ahujaesh/keeb/images/256x256.png

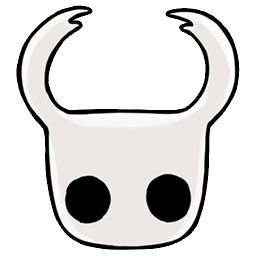
images/256x256.png
