ahujaesh/keeb/images/442066f4d0f0c367ef5b7a7e3e610547.jpg

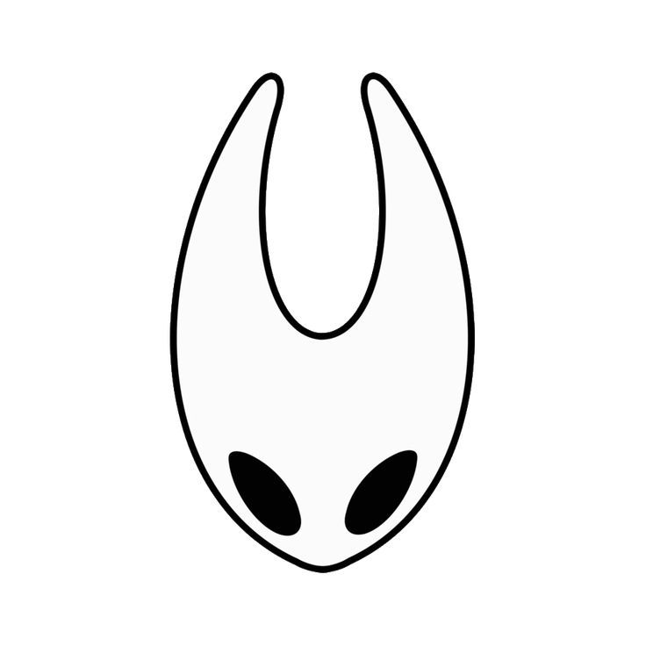
images/442066f4d0f0c367ef5b7a7e3e610547.jpg
