ahujaesh/keeb/images/Das_Shiekah_Auge_BoTW.png

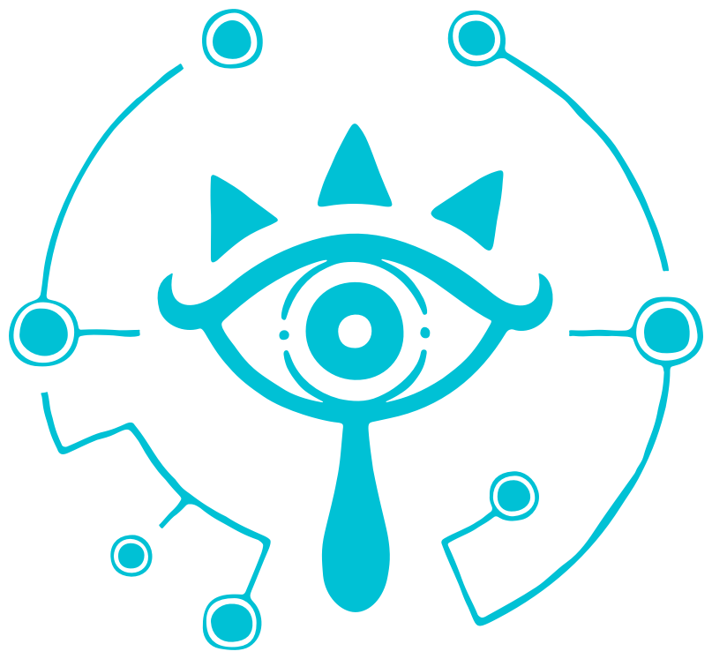
images/Das_Shiekah_Auge_BoTW.png
