ahujaesh/keeb/images/flag-standalone-wtransparent.png

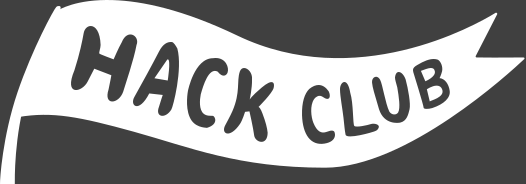
images/flag-standalone-wtransparent.png
