ahujaesh/keeb/marbastlib-main/marbastlib-main/resources/repolist.png

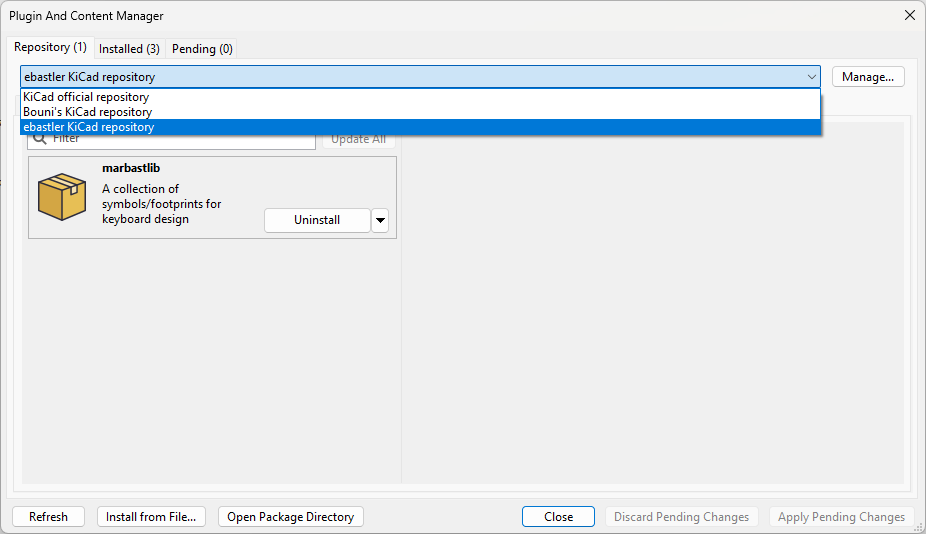
marbastlib-main/marbastlib-main/resources/repolist.png
