ahujaesh/keeb/misc/usb-a-female-2.snapshot.1/модуль USB A (2).JPG

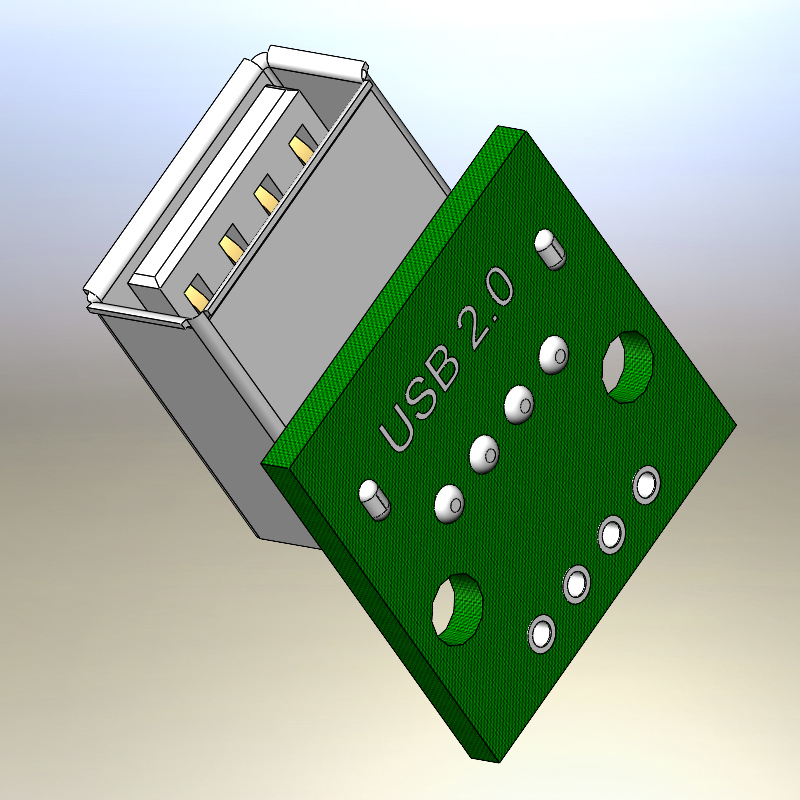
misc/usb-a-female-2.snapshot.1/модуль USB A (2).JPG
