ahujaesh/keeb/misc/usb-type-a-connector-2.snapshot.1/USB_Type_A rear.png

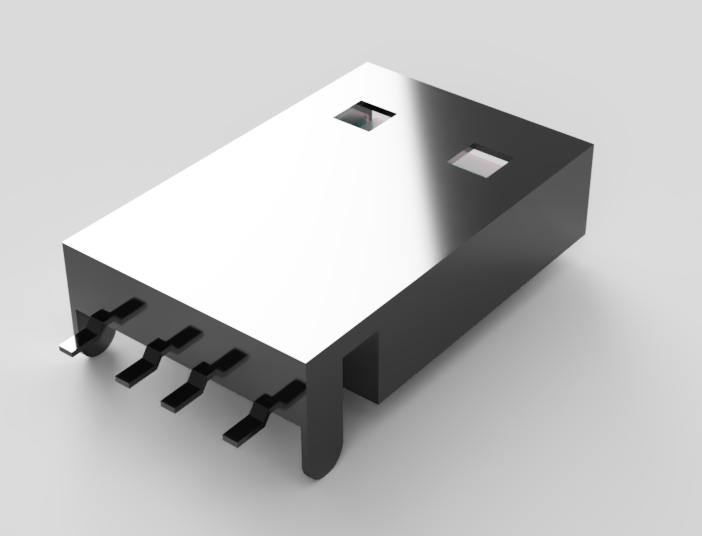
misc/usb-type-a-connector-2.snapshot.1/USB_Type_A rear.png
