ahujaesh/keeb/misc/usb-type-c-port-2.snapshot.1/USB Type C Port.png

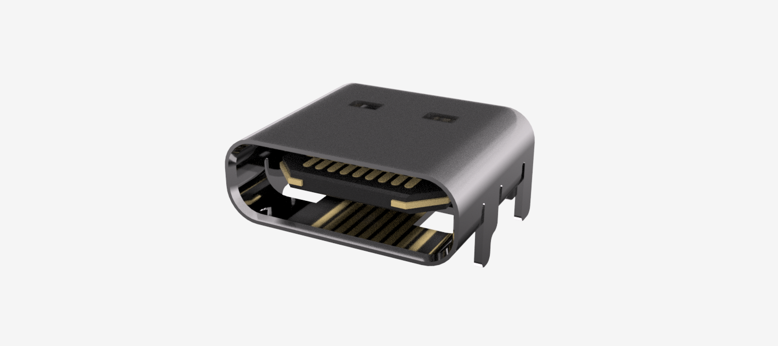
misc/usb-type-c-port-2.snapshot.1/USB Type C Port.png
