ahujaesh/keeb/misc/complete-cherry-mx-stem-keycap-set-optimized-for-3d-printing-gem-profile-multi-material-model_files/2.25U_ShiftyShiftL.3mf

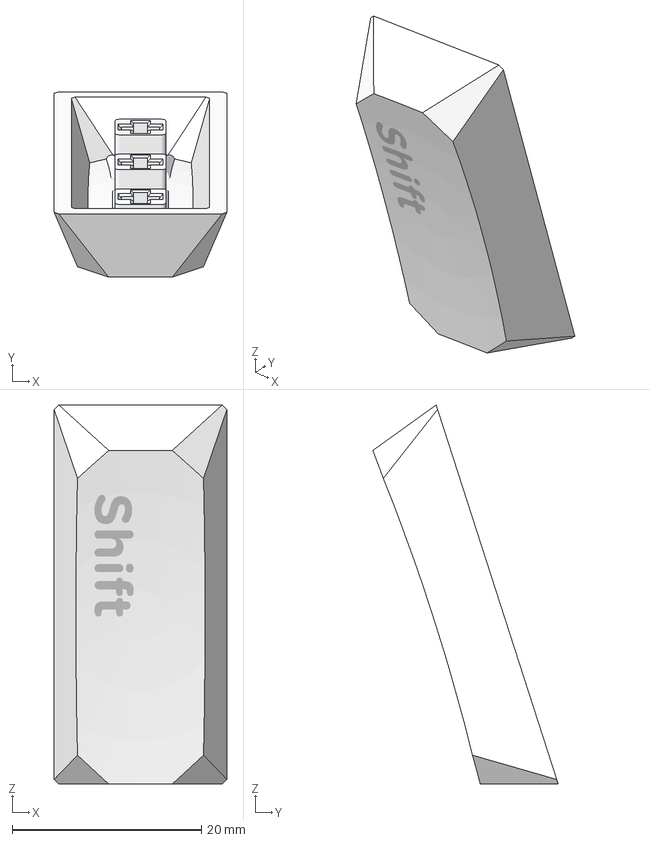
[picture p38: CAD file, 2025-10-08]
misc/complete-cherry-mx-stem-keycap-set-optimized-for-3d-printing-gem-profile-multi-material-model_files/2.25U_ShiftyShiftL.3mf
18.2 x 19.6 x 40.0 mm
