ahujaesh/keeb/marbastlib-main/marbastlib-main/3dmodels/CON_SM08B-SRSS-TB.step

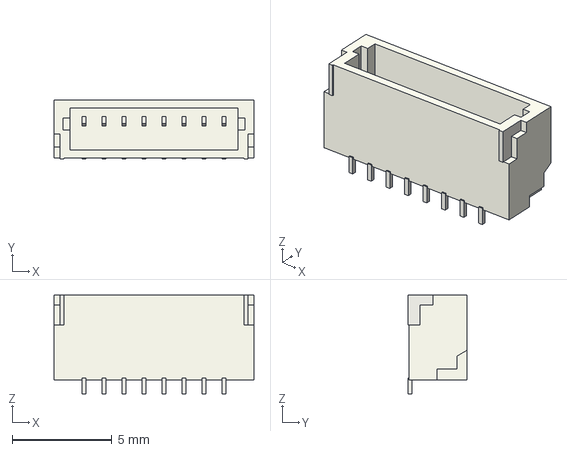
[picture p40: CAD file, 2025-10-04]
marbastlib-main/marbastlib-main/3dmodels/CON_SM08B-SRSS-TB.step
10.0 x 2.96 x 4.95 mm
