ahujaesh/keeb/marbastlib-main/marbastlib-main/3dmodels/CON_781710005.step

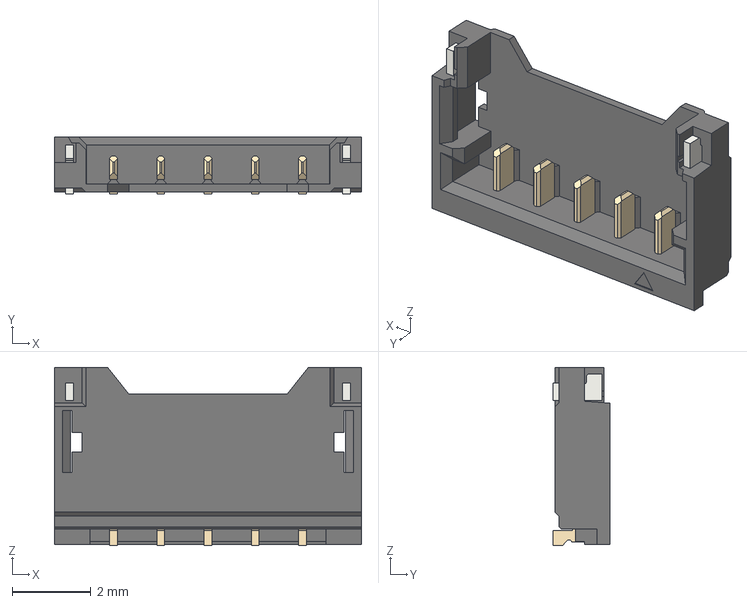
[picture p41: CAD file, 2025-10-04]
marbastlib-main/marbastlib-main/3dmodels/CON_781710005.step
7.80 x 1.45 x 4.53 mm
