ahujaesh/keeb/marbastlib-main/marbastlib-main/3dmodels/CON_2121340005.step

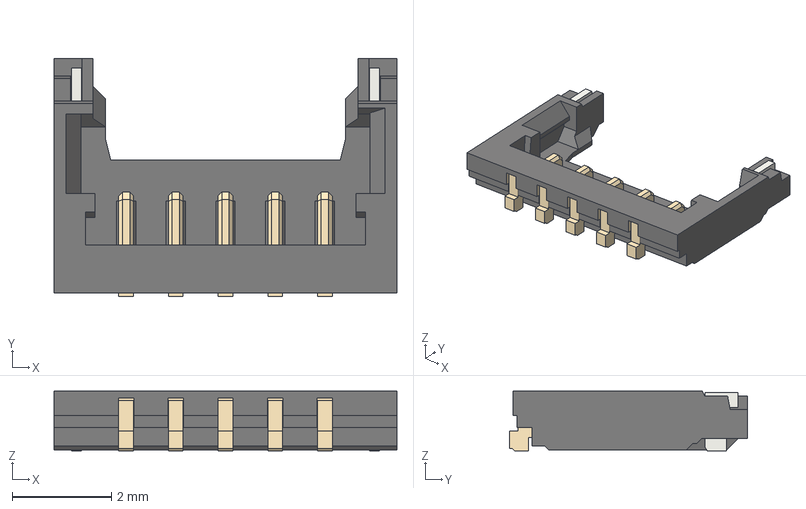
[picture p42: CAD file, 2025-10-04]
marbastlib-main/marbastlib-main/3dmodels/CON_2121340005.step
6.90 x 4.79 x 1.20 mm
