ahujaesh/keeb/marbastlib-main/marbastlib-main/3dmodels/HS_CPG135001S30_Choc.step

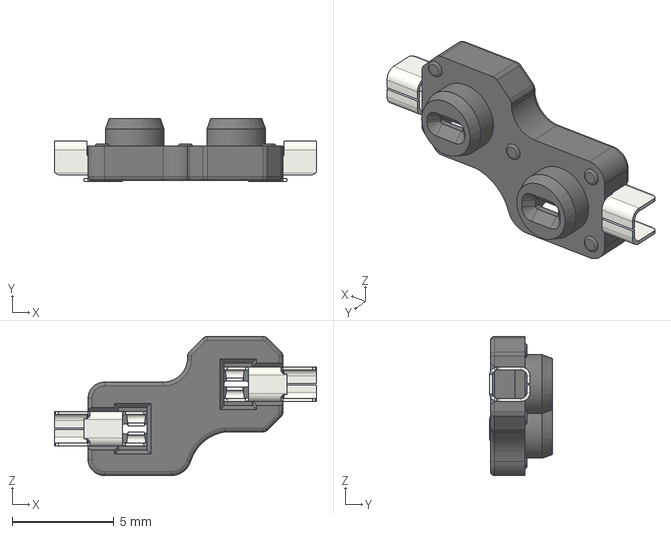
[picture p43: CAD file, 2025-10-04]
marbastlib-main/marbastlib-main/3dmodels/HS_CPG135001S30_Choc.step
12.9 x 3.09 x 6.85 mm
pin x 2
socket
