ahujaesh/keeb/marbastlib-main/marbastlib-main/3dmodels/CON_HytePro_M411P_Plug_1x04.step

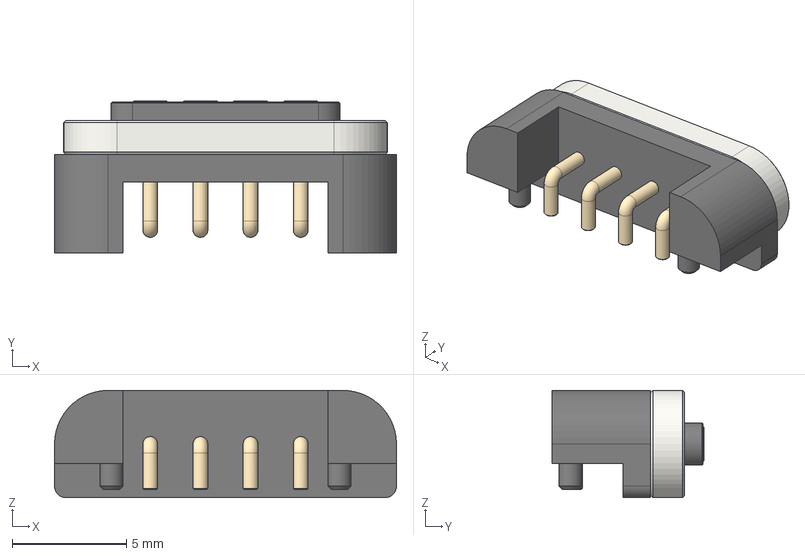
[picture p44: CAD file, 2025-10-04]
marbastlib-main/marbastlib-main/3dmodels/CON_HytePro_M411P_Plug_1x04.step
15.0 x 6.64 x 4.70 mm
Magnetic Connector Male - MiddlePart
Magnetic Connector Male - MountingPart
Magnetic Connector Male-tip_Standard
