ahujaesh/keeb/misc/complete-cherry-mx-stem-keycap-set-optimized-for-3d-printing-gem-profile-multi-material-model_files/numpad5.3mf

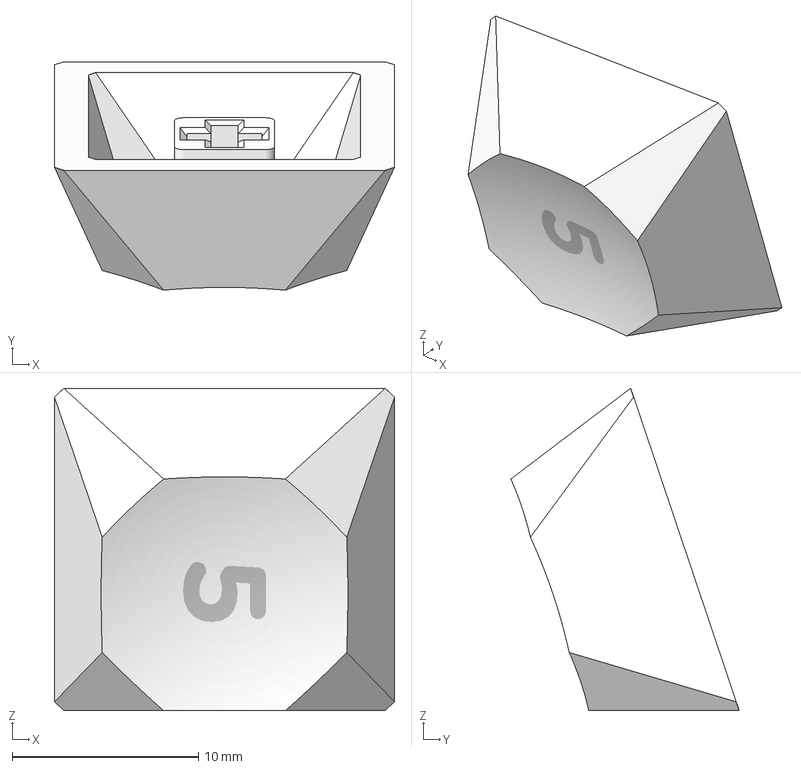
[picture p46: CAD file, 2025-10-08]
misc/complete-cherry-mx-stem-keycap-set-optimized-for-3d-printing-gem-profile-multi-material-model_files/numpad5.3mf
18.2 x 12.3 x 17.3 mm
