ahujaesh/keeb/marbastlib-main/marbastlib-main/3dmodels/CON_2082940030.step

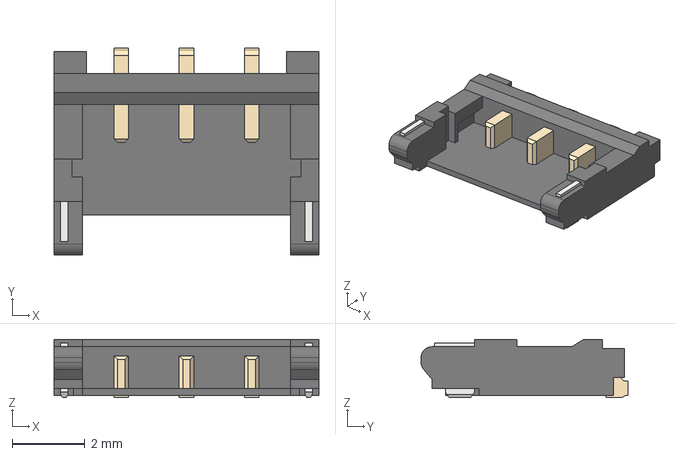
[picture p47: CAD file, 2025-10-04]
marbastlib-main/marbastlib-main/3dmodels/CON_2082940030.step
7.30 x 5.70 x 1.60 mm
