ahujaesh/keeb/marbastlib-main/marbastlib-main/3dmodels/PNT_RKJXU1210006.step

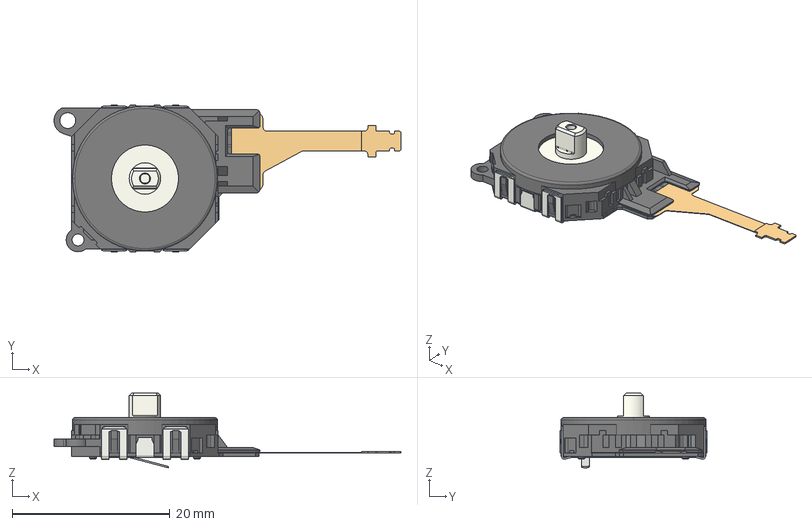
[picture p48: CAD file, 2025-10-04]
marbastlib-main/marbastlib-main/3dmodels/PNT_RKJXU1210006.step
44.0 x 18.6 x 9.50 mm
