ahujaesh/keeb/marbastlib-main/marbastlib-main/3dmodels/SW_ESP3020.step

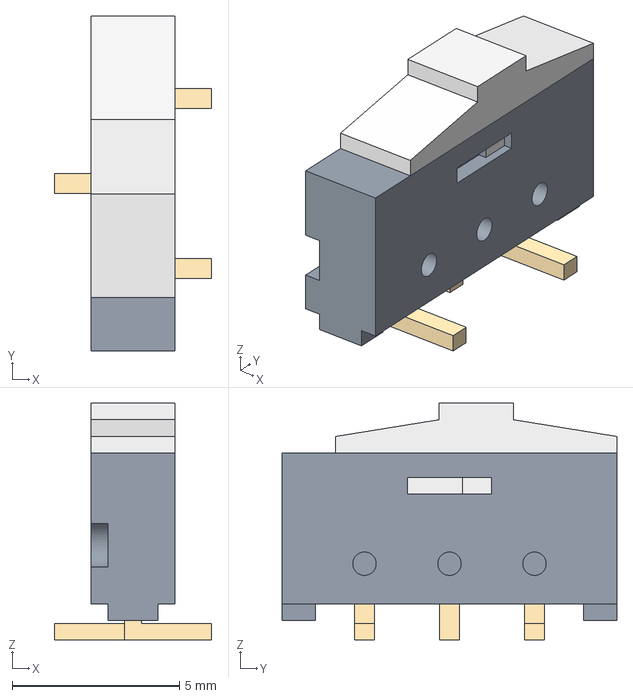
[picture p49: CAD file, 2025-10-04]
marbastlib-main/marbastlib-main/3dmodels/SW_ESP3020.step
4.70 x 10.0 x 7.08 mm
