ahujaesh/keeb/misc/complete-cherry-mx-stem-keycap-set-optimized-for-3d-printing-gem-profile-multi-material-model_files/2U_blank.3mf

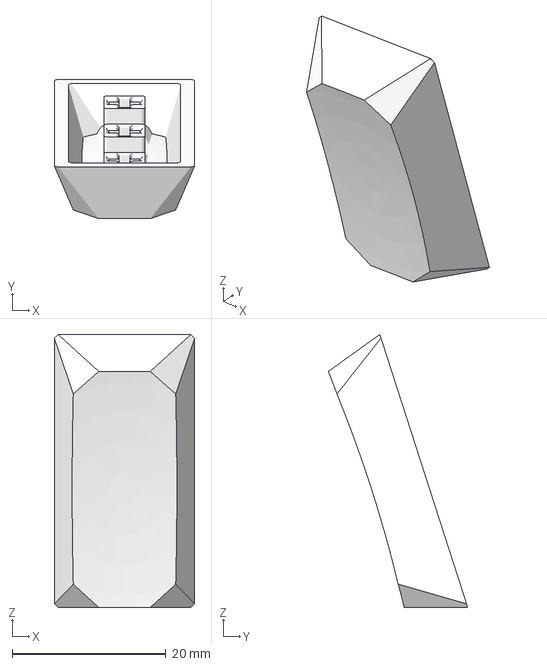
[picture p50: CAD file, 2025-10-08]
misc/complete-cherry-mx-stem-keycap-set-optimized-for-3d-printing-gem-profile-multi-material-model_files/2U_blank.3mf
18.2 x 18.1 x 35.5 mm
