ahujaesh/keeb/marbastlib-main/marbastlib-main/3dmodels/CON_2082940020.step

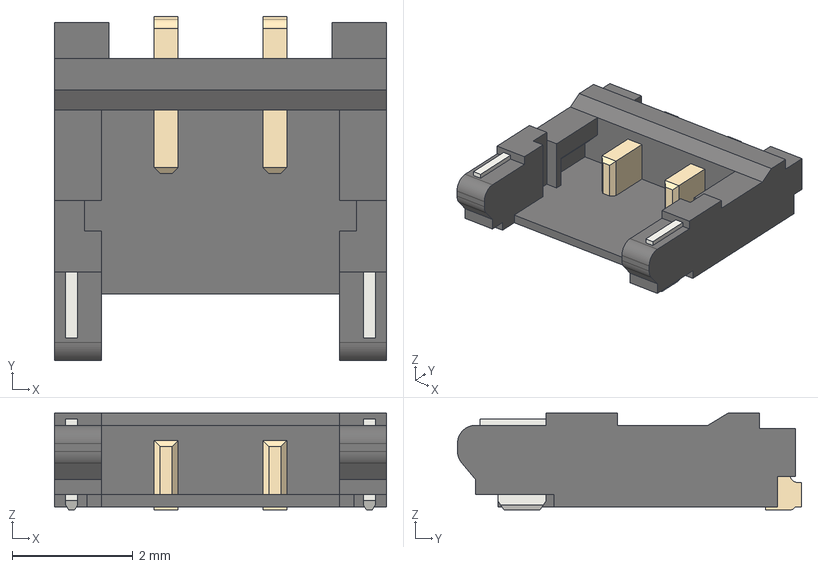
[picture p51: CAD file, 2025-10-04]
marbastlib-main/marbastlib-main/3dmodels/CON_2082940020.step
5.50 x 5.70 x 1.60 mm
