ahujaesh/keeb/marbastlib-main/marbastlib-main/3dmodels/L_Bourns_SRP6060FA.step

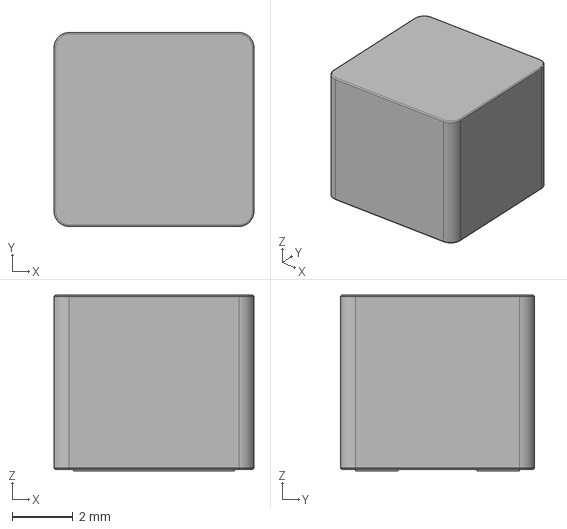
[picture p52: CAD file, 2025-10-04]
marbastlib-main/marbastlib-main/3dmodels/L_Bourns_SRP6060FA.step
6.60 x 6.40 x 5.80 mm
