ahujaesh/keeb/marbastlib-main/marbastlib-main/3dmodels/CON_781710003.step

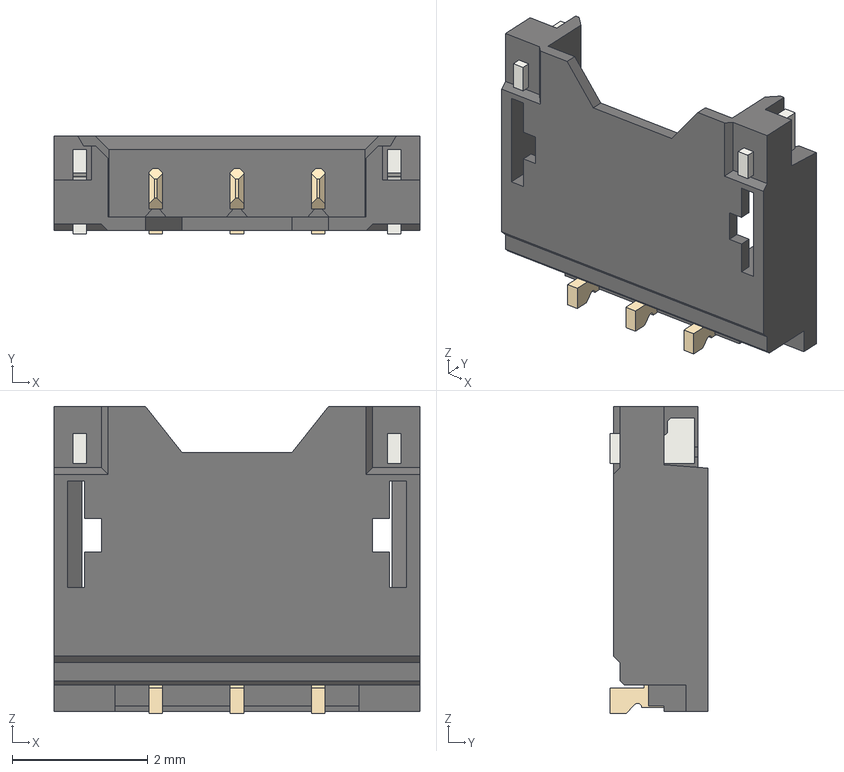
[picture p54: CAD file, 2025-10-04]
marbastlib-main/marbastlib-main/3dmodels/CON_781710003.step
5.40 x 1.45 x 4.53 mm
