ahujaesh/keeb/marbastlib-main/marbastlib-main/3dmodels/ROT_SKYLOONG_HS.step

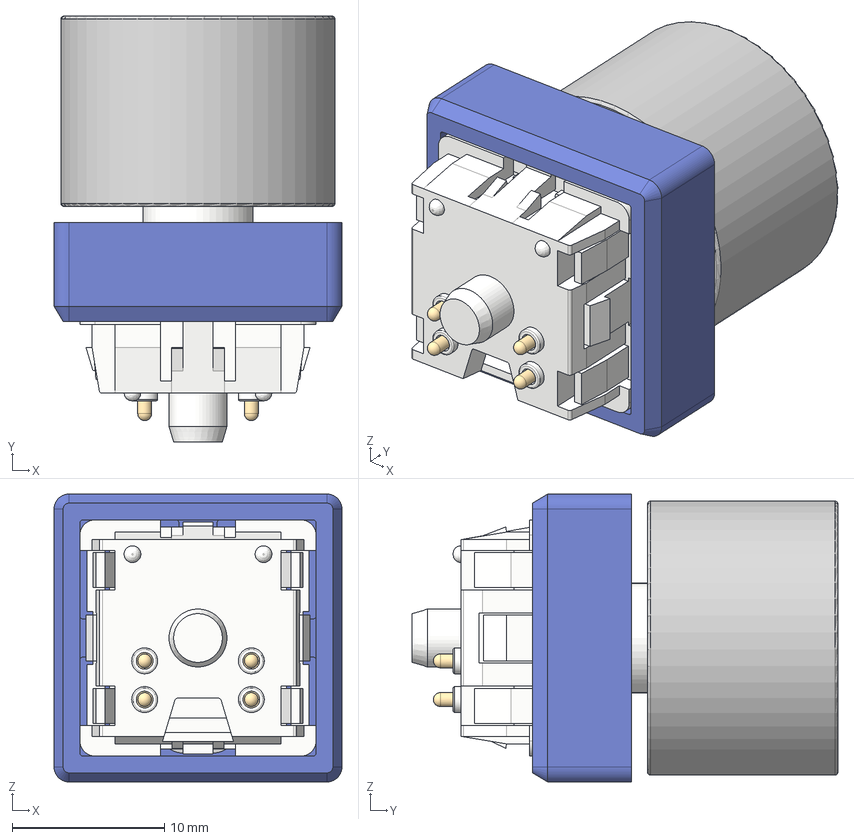
[picture p56: CAD file, 2025-10-04]
marbastlib-main/marbastlib-main/3dmodels/ROT_SKYLOONG_HS.step
18.9 x 27.9 x 18.9 mm
Top
Shaft
Pogo Pin x 4
Bottom
Top_1
Cover
Knob
