ahujaesh/keeb/misc/complete-cherry-mx-stem-keycap-set-optimized-for-3d-printing-gem-profile-multi-material-model_files/1.5U_LAlt.3mf

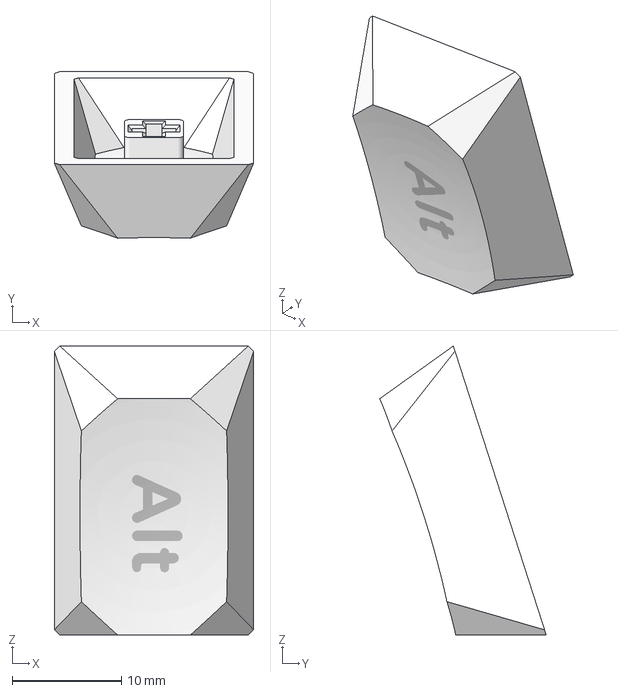
[picture p58: CAD file, 2025-10-08]
misc/complete-cherry-mx-stem-keycap-set-optimized-for-3d-printing-gem-profile-multi-material-model_files/1.5U_LAlt.3mf
18.2 x 15.2 x 26.4 mm
