ahujaesh/keeb/marbastlib-main/marbastlib-main/3dmodels/QFN-22_MP2722.step

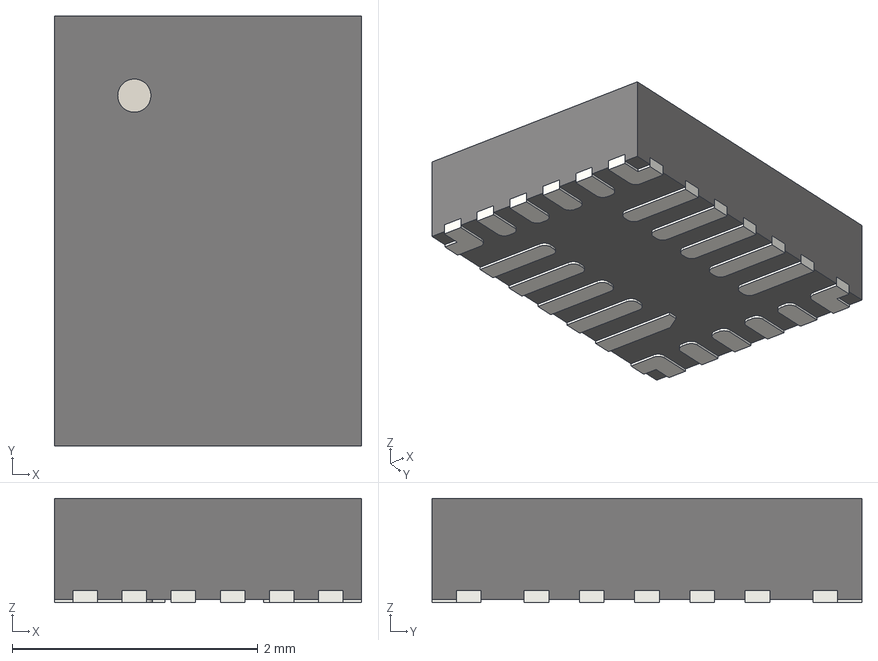
[picture p59: CAD file, 2025-10-04]
marbastlib-main/marbastlib-main/3dmodels/QFN-22_MP2722.step
2.50 x 3.50 x 0.85 mm
