ahujaesh/keeb/misc/complete-cherry-mx-stem-keycap-set-optimized-for-3d-printing-gem-profile-multi-material-model_files/1.25U_CommandSymbol.3mf

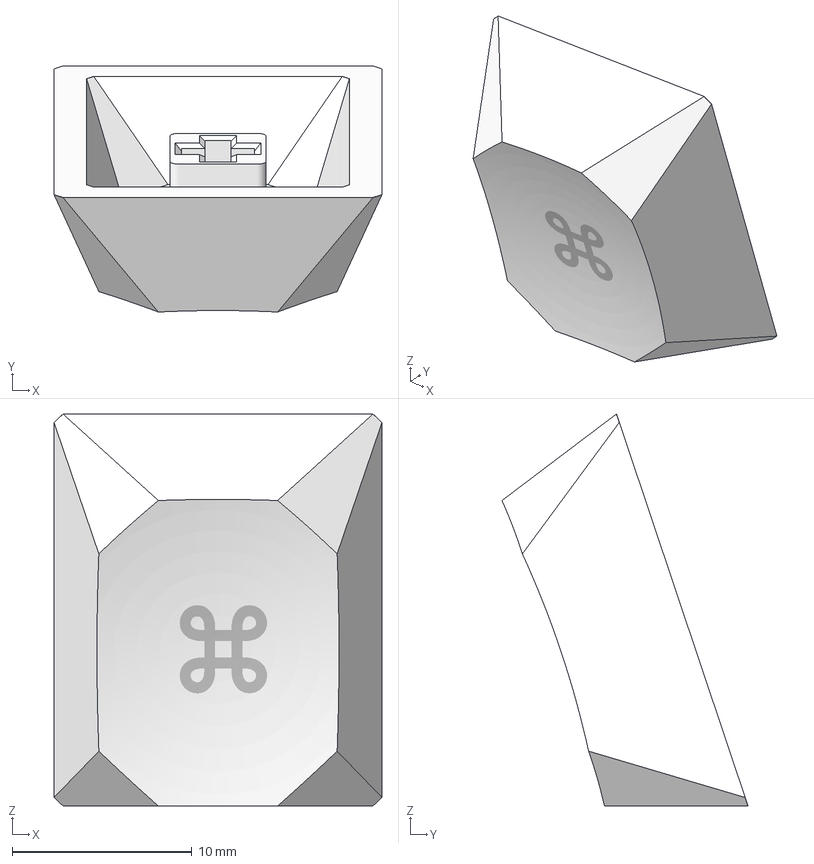
[picture p60: CAD file, 2025-10-08]
misc/complete-cherry-mx-stem-keycap-set-optimized-for-3d-printing-gem-profile-multi-material-model_files/1.25U_CommandSymbol.3mf
18.2 x 13.7 x 21.8 mm
