ahujaesh/keeb/marbastlib-main/marbastlib-main/3dmodels/CON_XUNPU_FPC-05F-24PH20.step

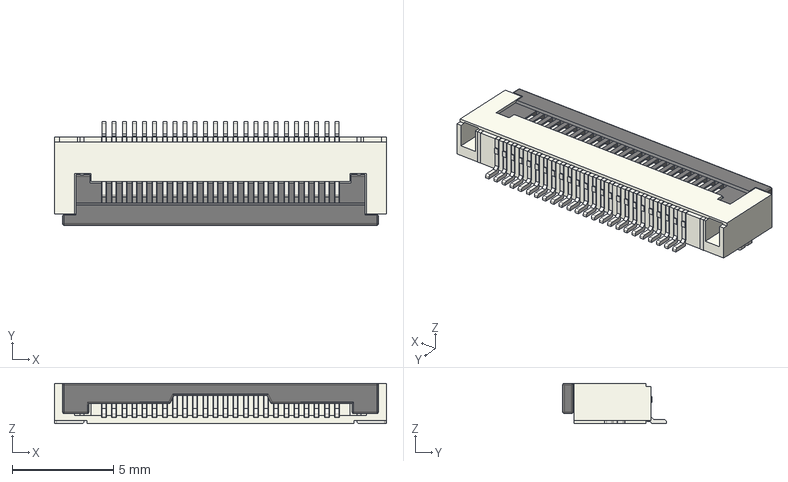
[picture p61: CAD file, 2025-10-04]
marbastlib-main/marbastlib-main/3dmodels/CON_XUNPU_FPC-05F-24PH20.step
16.4 x 5.12 x 2.00 mm
Board
