ahujaesh/keeb/marbastlib-main/marbastlib-main/3dmodels/CON_781710004.step

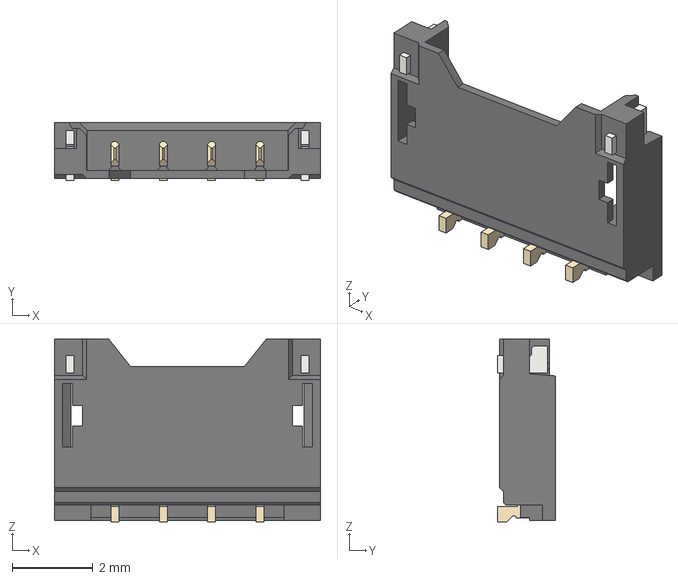
[picture p62: CAD file, 2025-10-04]
marbastlib-main/marbastlib-main/3dmodels/CON_781710004.step
6.60 x 1.45 x 4.53 mm
