ahujaesh/keeb/marbastlib-main/marbastlib-main/3dmodels/CON_781715006.step

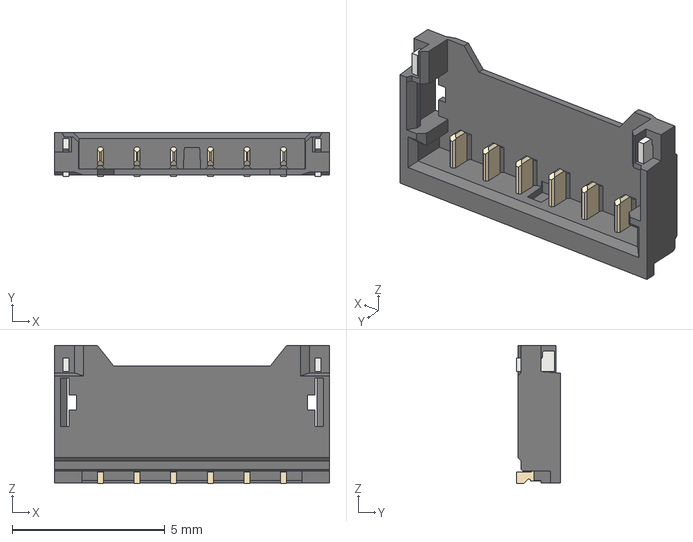
[picture p63: CAD file, 2025-10-04]
marbastlib-main/marbastlib-main/3dmodels/CON_781715006.step
9.00 x 1.45 x 4.53 mm
