ahujaesh/keeb/marbastlib-main/marbastlib-main/3dmodels/CON_781710002.step

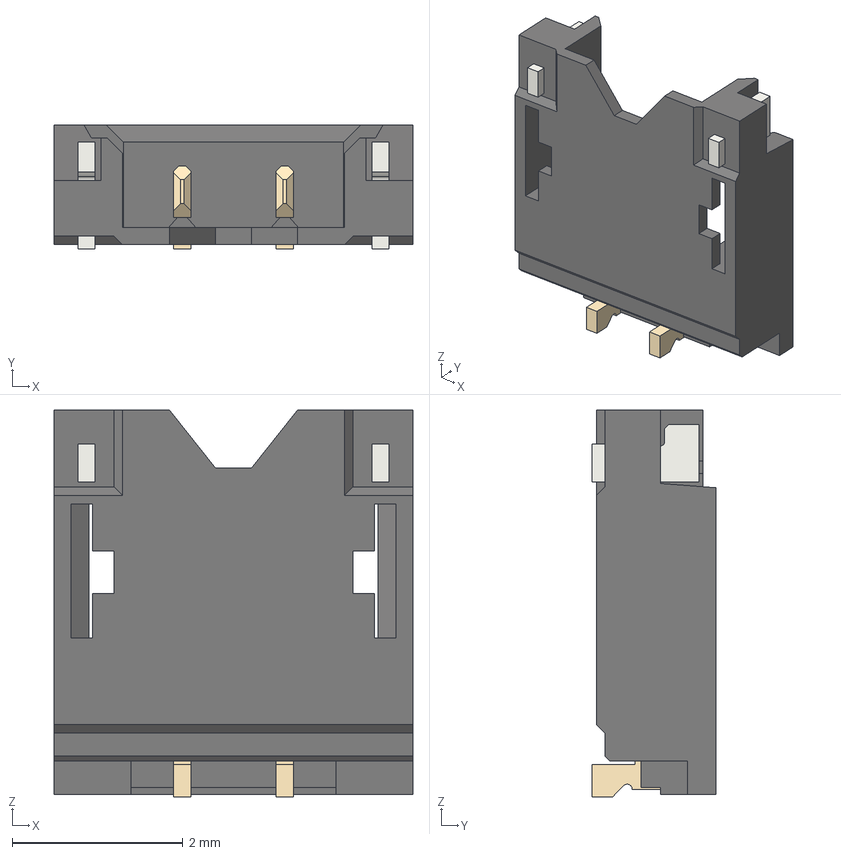
[picture p64: CAD file, 2025-10-04]
marbastlib-main/marbastlib-main/3dmodels/CON_781710002.step
4.20 x 1.45 x 4.53 mm
