ahujaesh/keeb/marbastlib-main/marbastlib-main/3dmodels/SW_SSSS223900.step

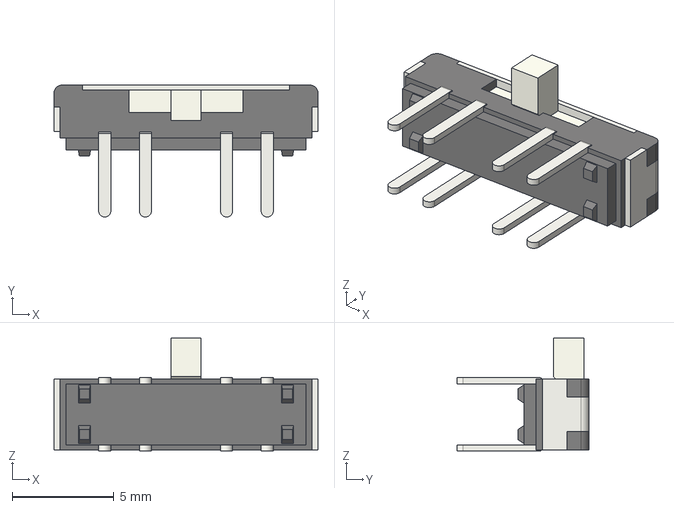
[picture p65: CAD file, 2025-10-04]
marbastlib-main/marbastlib-main/3dmodels/SW_SSSS223900.step
13.0 x 6.50 x 5.55 mm
