ahujaesh/keeb/marbastlib-main/marbastlib-main/3dmodels/L_Bourns_SRP6050CA.step

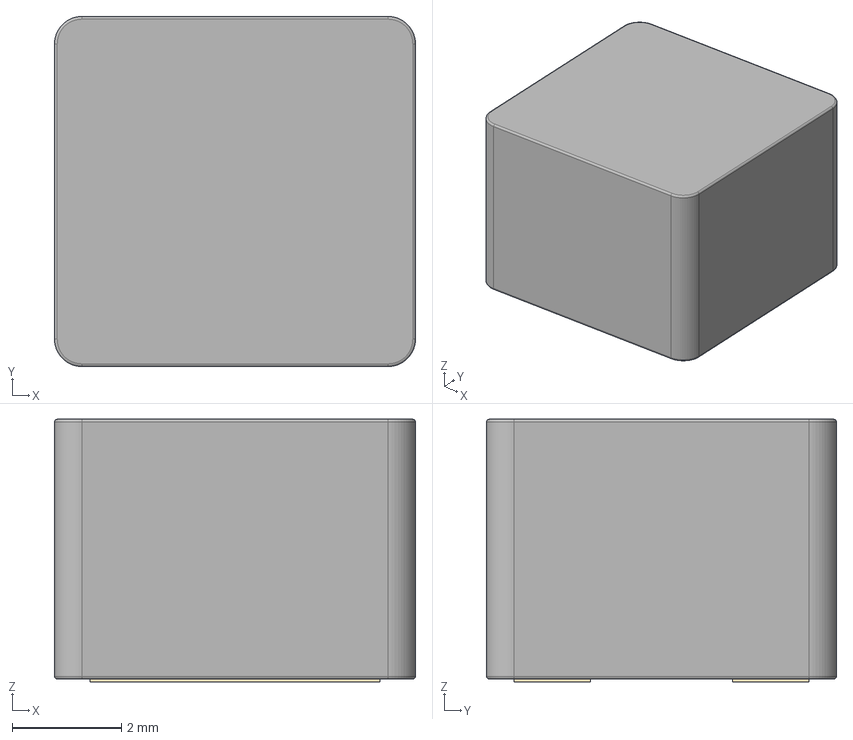
[picture p67: CAD file, 2025-10-04]
marbastlib-main/marbastlib-main/3dmodels/L_Bourns_SRP6050CA.step
6.60 x 6.40 x 4.80 mm
