ahujaesh/keeb/marbastlib-main/marbastlib-main/3dmodels/PNT_psp1000.step

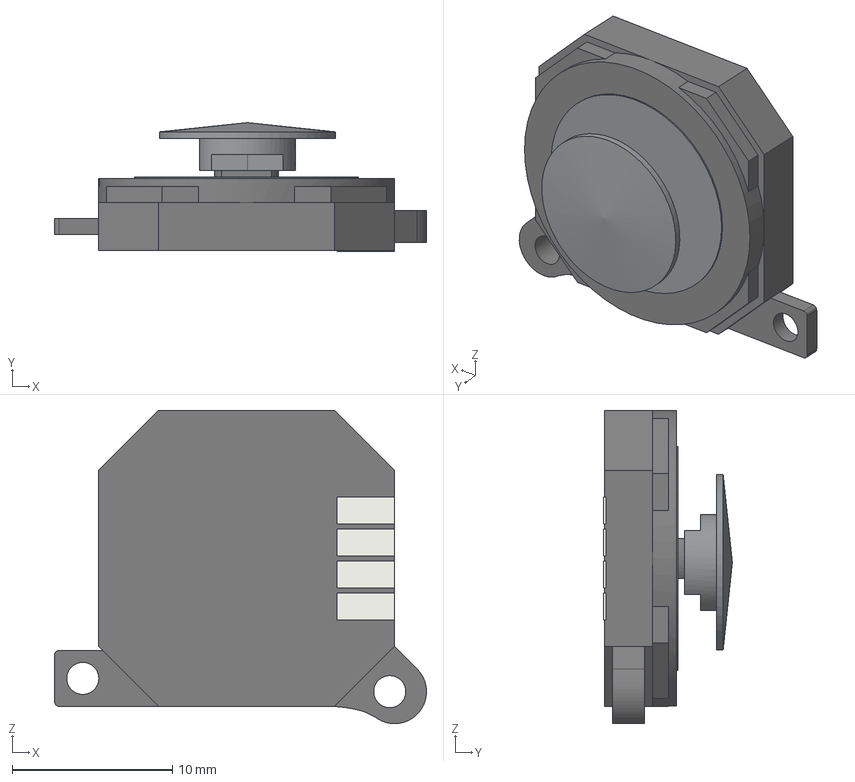
[picture p68: CAD file, 2025-10-04]
marbastlib-main/marbastlib-main/3dmodels/PNT_psp1000.step
23.2 x 8.05 x 19.6 mm
