ahujaesh/keeb/marbastlib-main/marbastlib-main/3dmodels/Liatris.step

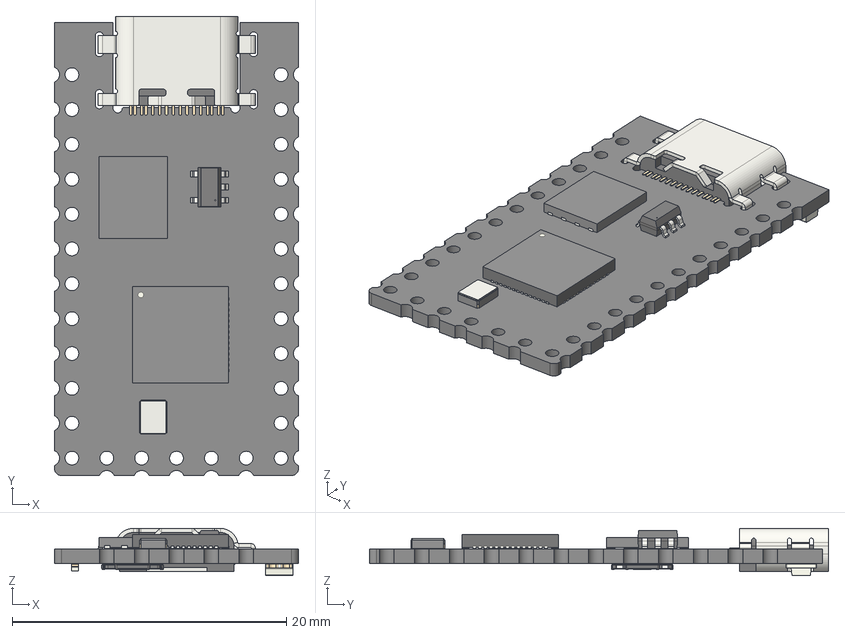
[picture p69: CAD file, 2025-10-04]
marbastlib-main/marbastlib-main/3dmodels/Liatris.step
17.8 x 33.5 x 3.44 mm
RP2040 PCB
