ahujaesh/keeb/marbastlib-main/marbastlib-main/3dmodels/LED_SK6812MINI-E.step

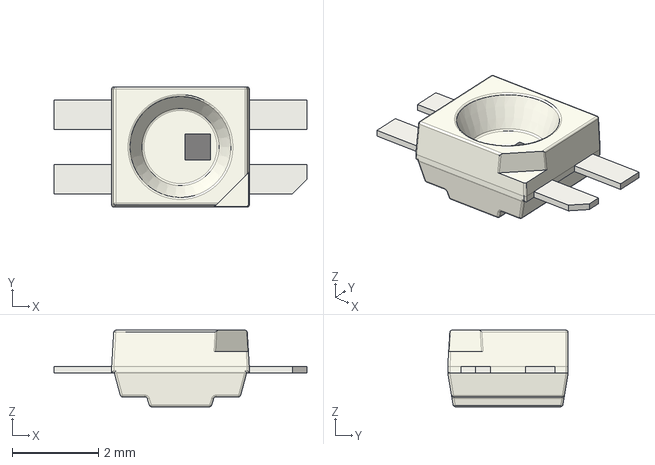
[picture p71: CAD file, 2025-10-04]
marbastlib-main/marbastlib-main/3dmodels/LED_SK6812MINI-E.step
5.88 x 2.80 x 1.78 mm
