ahujaesh/keeb/marbastlib-main/marbastlib-main/3dmodels/SW_SKHLLC.step

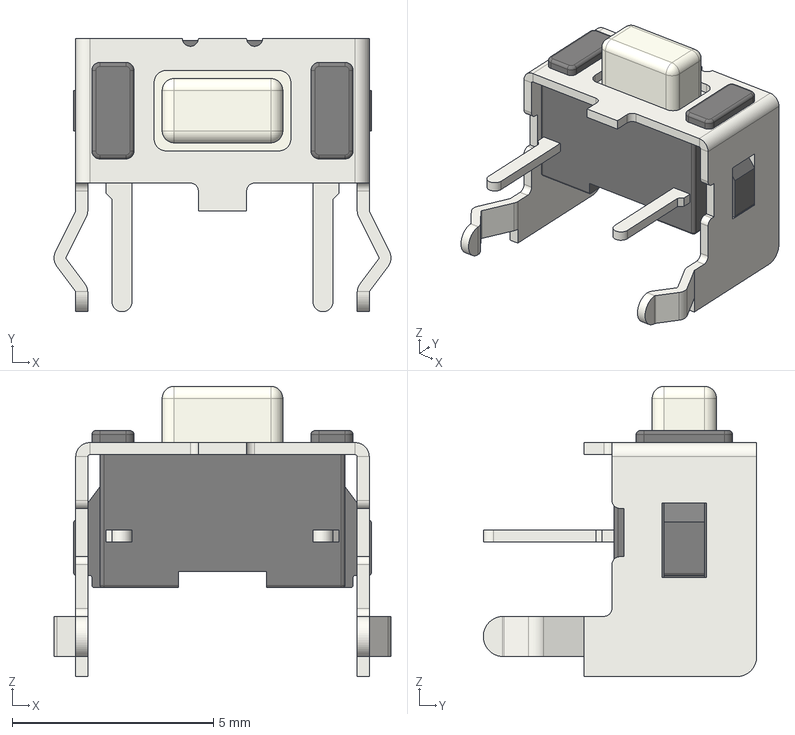
[picture p72: CAD file, 2025-10-04]
marbastlib-main/marbastlib-main/3dmodels/SW_SKHLLC.step
8.38 x 6.80 x 7.22 mm
