ahujaesh/keeb/marbastlib-main/marbastlib-main/3dmodels/CON_2082940050.step

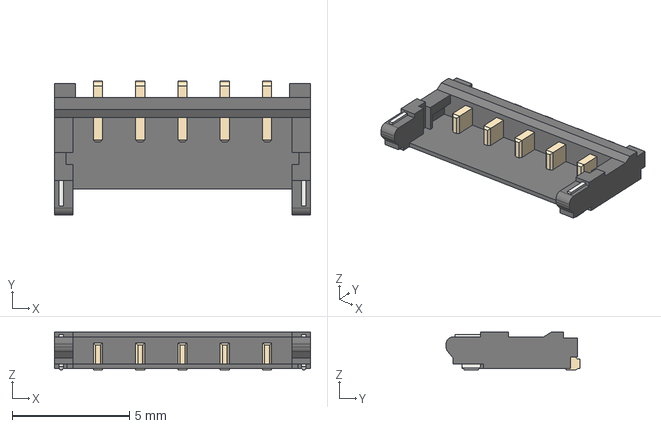
[picture p74: CAD file, 2025-10-04]
marbastlib-main/marbastlib-main/3dmodels/CON_2082940050.step
10.9 x 5.70 x 1.60 mm
