ahujaesh/keeb/marbastlib-main/marbastlib-main/3dmodels/CON_SM02B-SRSS-TB.step

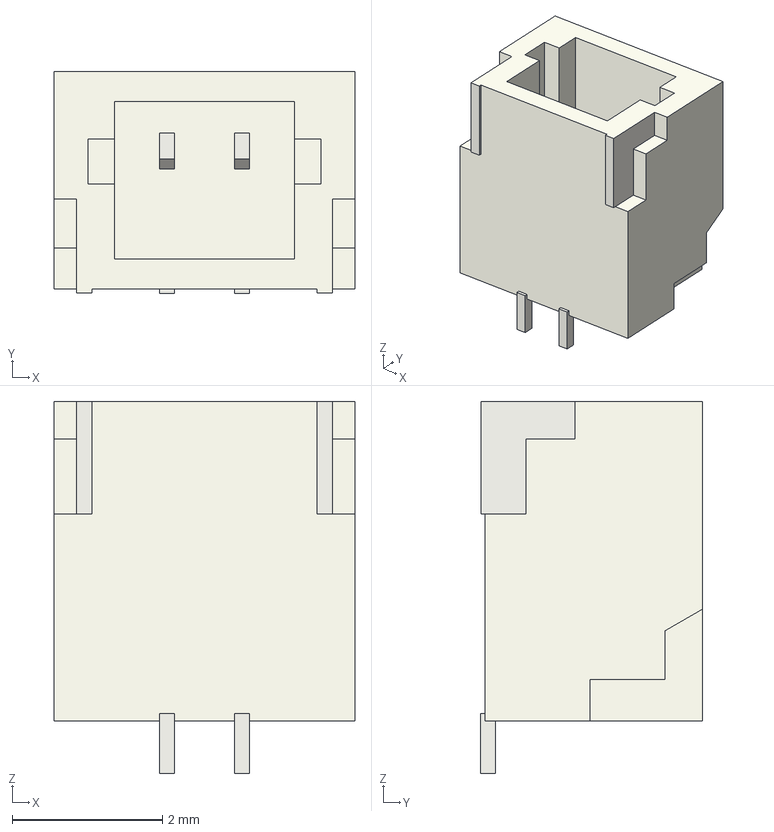
[picture p75: CAD file, 2025-10-04]
marbastlib-main/marbastlib-main/3dmodels/CON_SM02B-SRSS-TB.step
4.00 x 2.96 x 4.95 mm
