ahujaesh/keeb/marbastlib-main/marbastlib-main/3dmodels/PDFN3.3x3.3.step

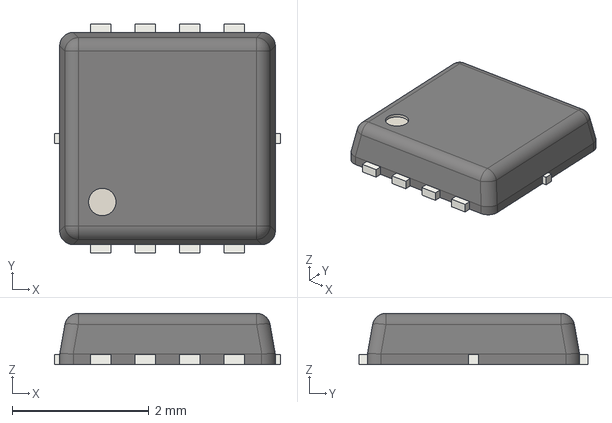
[picture p76: CAD file, 2025-10-04]
marbastlib-main/marbastlib-main/3dmodels/PDFN3.3x3.3.step
3.30 x 3.35 x 0.75 mm
