ahujaesh/keeb/marbastlib-main/marbastlib-main/3dmodels/Crystal_FA-128.step

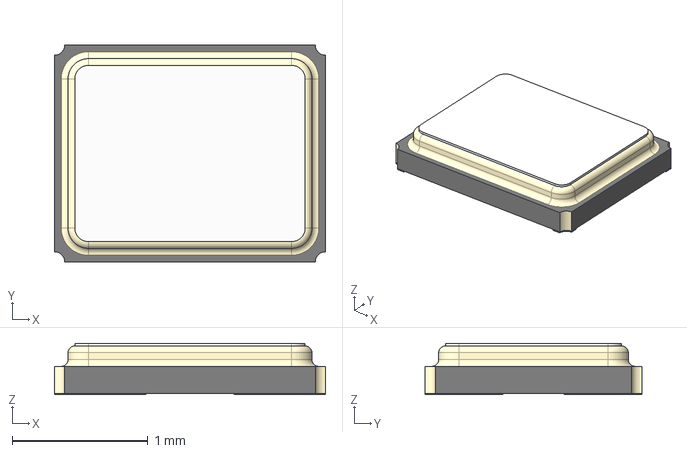
[picture p77: CAD file, 2025-10-04]
marbastlib-main/marbastlib-main/3dmodels/Crystal_FA-128.step
2.00 x 1.60 x 0.38 mm
