ahujaesh/keeb/marbastlib-main/marbastlib-main/3dmodels/HS_KS-2P02B01-01_MX.step

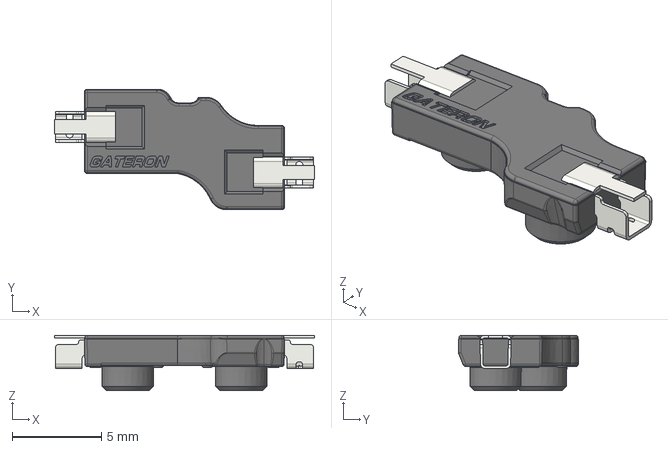
[picture p78: CAD file, 2025-10-04]
marbastlib-main/marbastlib-main/3dmodels/HS_KS-2P02B01-01_MX.step
14.6 x 6.74 x 3.10 mm
