ahujaesh/keeb/marbastlib-main/marbastlib-main/3dmodels/CON_MJ-4PP-9.step

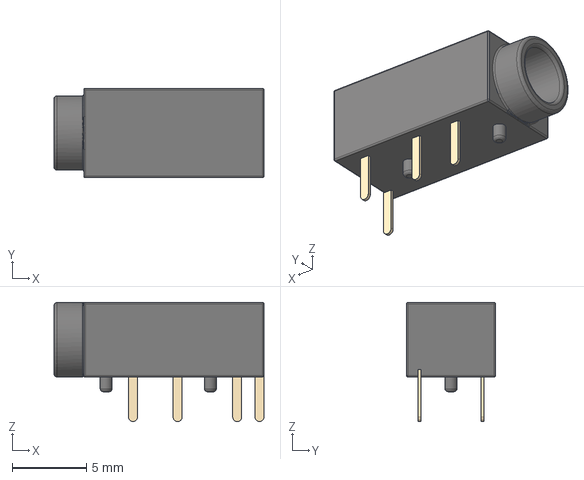
[picture p79: CAD file, 2025-10-04]
marbastlib-main/marbastlib-main/3dmodels/CON_MJ-4PP-9.step
14.1 x 6.00 x 8.00 mm
