ahujaesh/keeb/marbastlib-main/marbastlib-main/3dmodels/CON_HC-PBB40C-10DP-0.4V-02.step

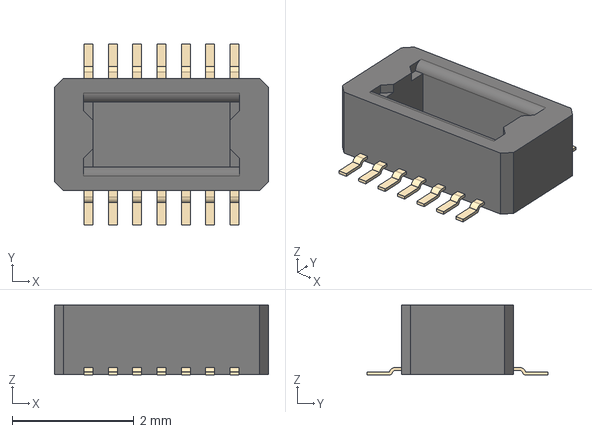
[picture p81: CAD file, 2025-10-04]
marbastlib-main/marbastlib-main/3dmodels/CON_HC-PBB40C-10DP-0.4V-02.step
3.52 x 2.97 x 1.15 mm
