ahujaesh/keeb/marbastlib-main/marbastlib-main/3dmodels/CON_SM04B-SRSS-TB.step

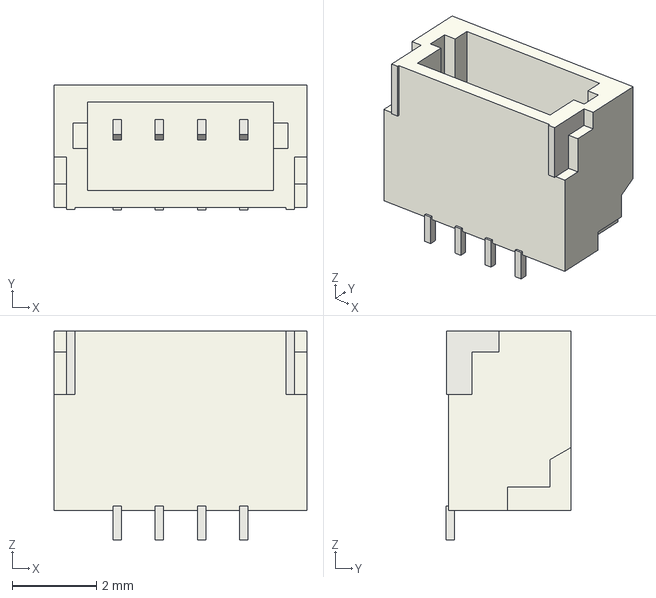
[picture p82: CAD file, 2025-10-04]
marbastlib-main/marbastlib-main/3dmodels/CON_SM04B-SRSS-TB.step
6.00 x 2.96 x 4.95 mm
