ahujaesh/keeb/marbastlib-main/marbastlib-main/3dmodels/SW_SSSS213100.step

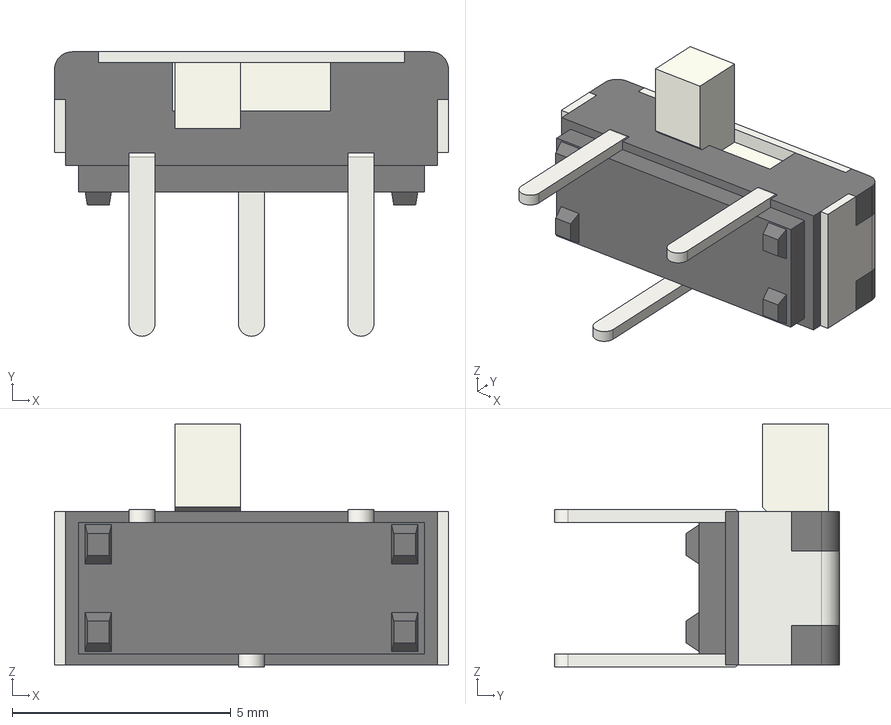
[picture p83: CAD file, 2025-10-04]
marbastlib-main/marbastlib-main/3dmodels/SW_SSSS213100.step
9.00 x 6.50 x 5.55 mm
