ahujaesh/keeb/marbastlib-main/marbastlib-main/3dmodels/LED_WS2812B-MINI.step

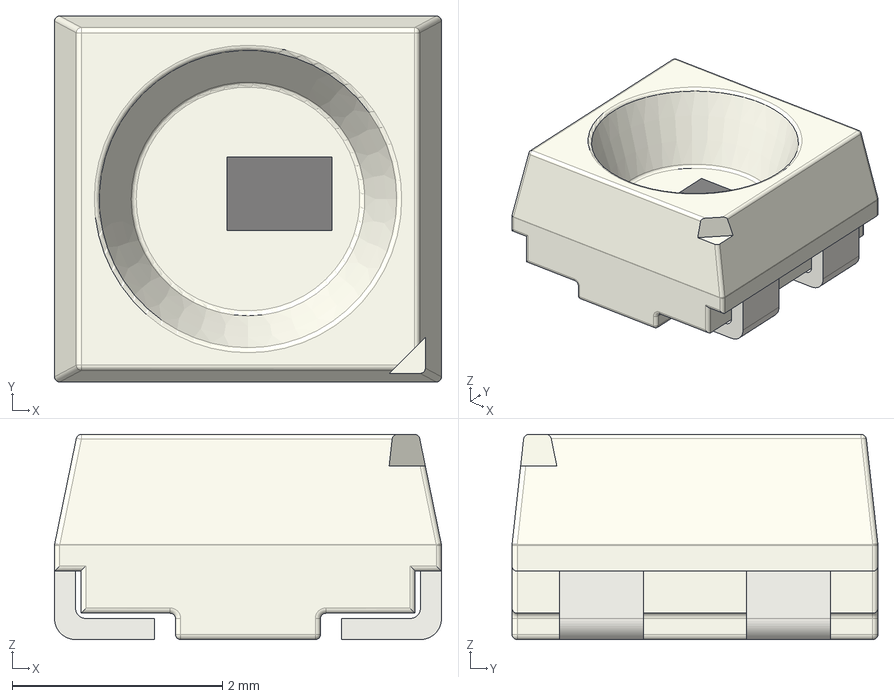
[picture p84: CAD file, 2025-10-04]
marbastlib-main/marbastlib-main/3dmodels/LED_WS2812B-MINI.step
3.68 x 3.48 x 1.95 mm
