ahujaesh/keeb/marbastlib-main/marbastlib-main/3dmodels/LED_MHT151RGBCT.step

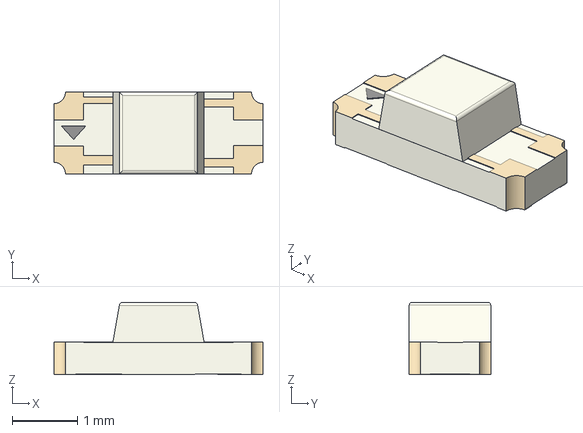
[picture p85: CAD file, 2025-10-04]
marbastlib-main/marbastlib-main/3dmodels/LED_MHT151RGBCT.step
3.20 x 1.25 x 1.11 mm
