ahujaesh/keeb/marbastlib-main/marbastlib-main/3dmodels/ROT_EC11N.step

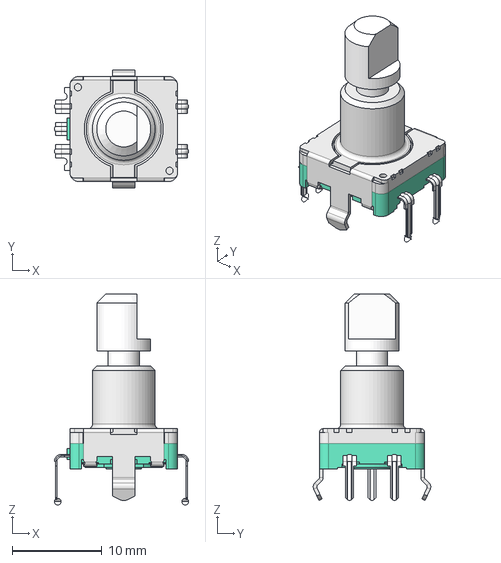
[picture p88: CAD file, 2025-10-04]
marbastlib-main/marbastlib-main/3dmodels/ROT_EC11N.step
14.9 x 13.1 x 23.5 mm
