ahujaesh/keeb/marbastlib-main/marbastlib-main/3dmodels/CON_SM13B-SRSS-TB.step

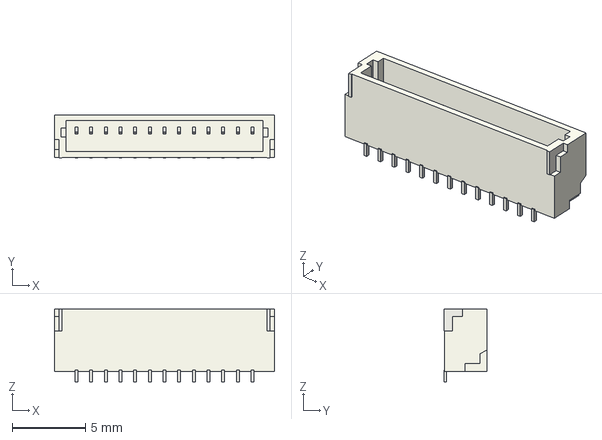
[picture p90: CAD file, 2025-10-04]
marbastlib-main/marbastlib-main/3dmodels/CON_SM13B-SRSS-TB.step
15.0 x 2.96 x 4.95 mm
