ahujaesh/keeb/marbastlib-main/marbastlib-main/3dmodels/L_Cenker_CKST353220.step

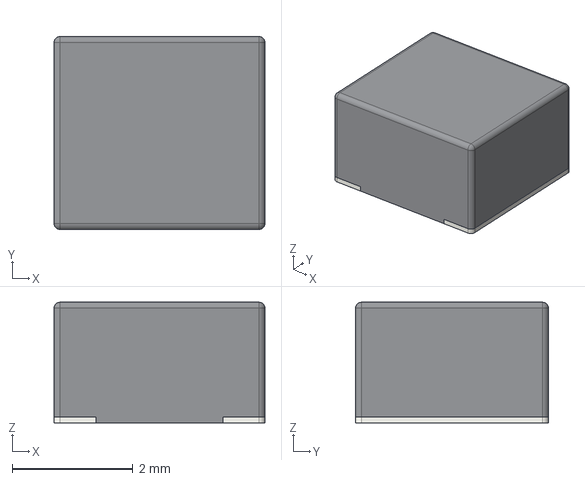
[picture p91: CAD file, 2025-10-04]
marbastlib-main/marbastlib-main/3dmodels/L_Cenker_CKST353220.step
3.50 x 3.20 x 2.00 mm
