ahujaesh/keeb/marbastlib-main/marbastlib-main/3dmodels/QFN-13_3x4mm_P0.5mm.step

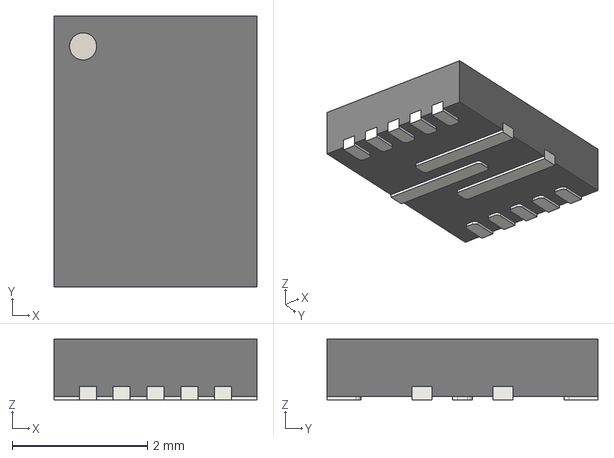
[picture p92: CAD file, 2025-10-04]
marbastlib-main/marbastlib-main/3dmodels/QFN-13_3x4mm_P0.5mm.step
3.00 x 4.00 x 0.9 mm
