ahujaesh/keeb/marbastlib-main/marbastlib-main/3dmodels/HS_KS-2P02B01-02_KS33.step

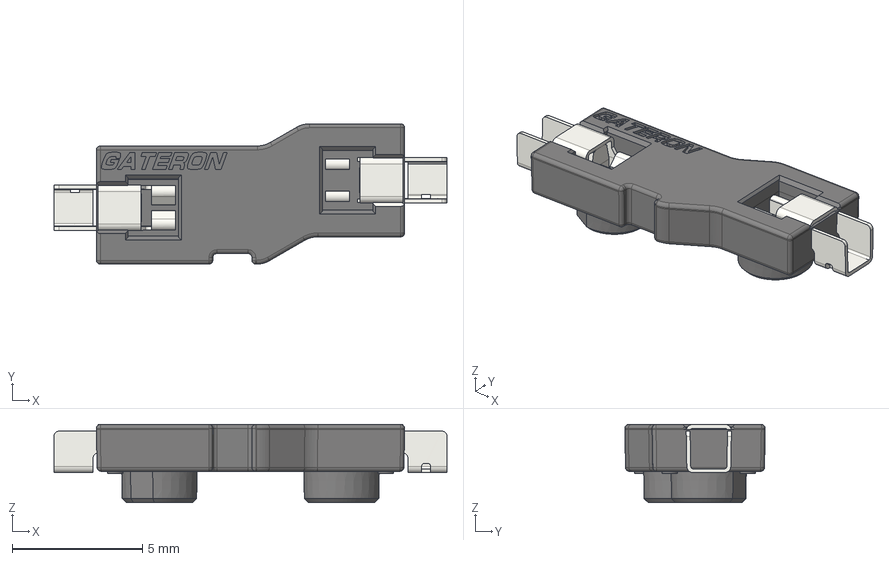
[picture p93: CAD file, 2025-10-04]
marbastlib-main/marbastlib-main/3dmodels/HS_KS-2P02B01-02_KS33.step
15.1 x 5.39 x 3.00 mm
