ahujaesh/keeb/marbastlib-main/marbastlib-main/3dmodels/CON_2082940040.step

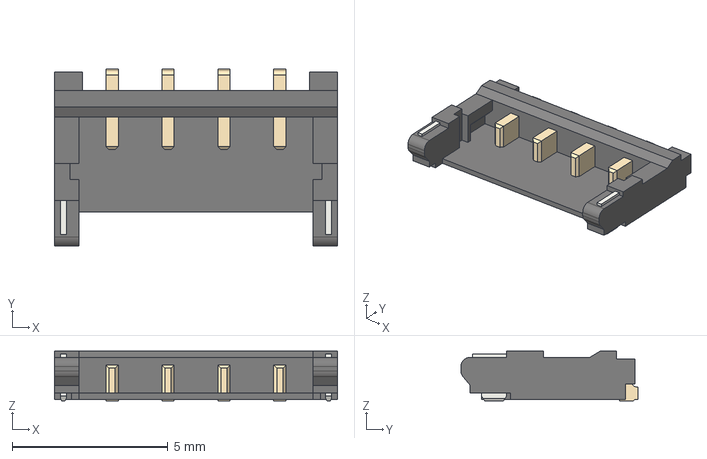
[picture p94: CAD file, 2025-10-04]
marbastlib-main/marbastlib-main/3dmodels/CON_2082940040.step
9.10 x 5.70 x 1.60 mm
