ahujaesh/keeb/marbastlib-main/marbastlib-main/3dmodels/SW_MSK12C02.step

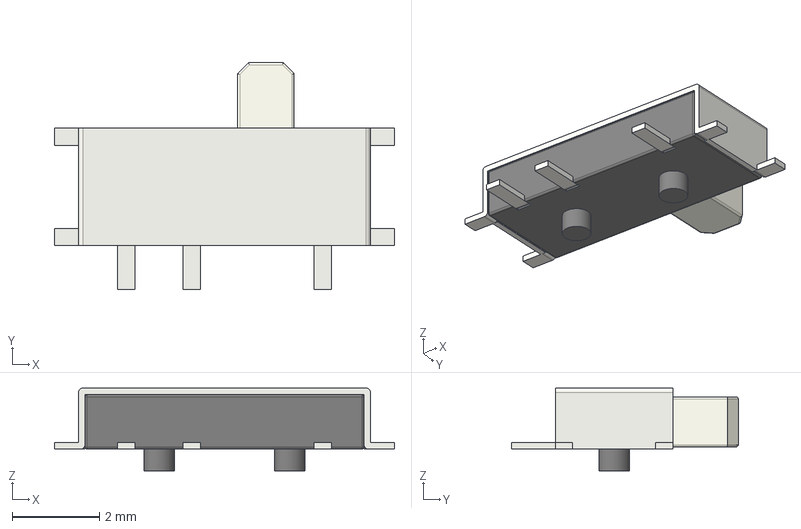
[picture p95: CAD file, 2025-10-04]
marbastlib-main/marbastlib-main/3dmodels/SW_MSK12C02.step
7.80 x 5.20 x 1.90 mm
