ahujaesh/keeb/marbastlib-main/marbastlib-main/3dmodels/ebyte_E73-2G4M08S1C.step

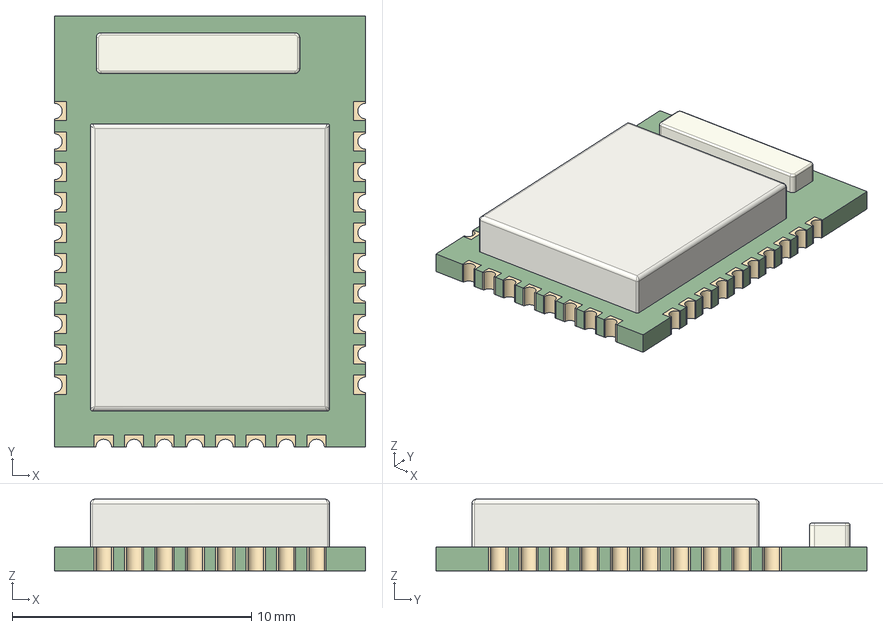
[picture p96: CAD file, 2025-10-04]
marbastlib-main/marbastlib-main/3dmodels/ebyte_E73-2G4M08S1C.step
13.0 x 18.0 x 3.00 mm
