ahujaesh/keeb/marbastlib-main/marbastlib-main/3dmodels/CON_TYPE-C-31-M-12.step

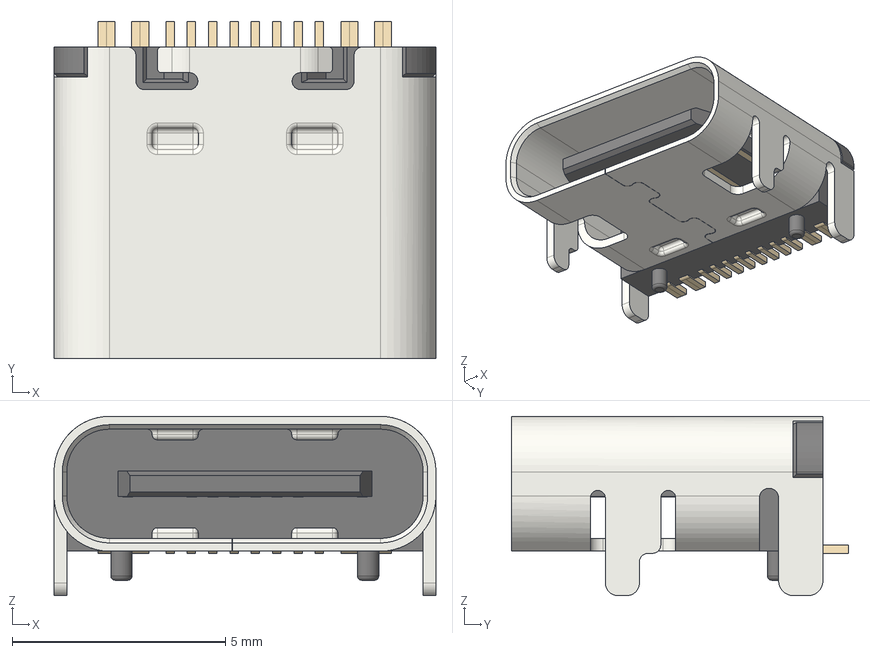
[picture p98: CAD file, 2025-10-04]
marbastlib-main/marbastlib-main/3dmodels/CON_TYPE-C-31-M-12.step
8.95 x 7.90 x 4.20 mm
ConPins
PcbPins
Mold
Frame
