ahujaesh/keeb/marbastlib-main/marbastlib-main/3dmodels/SW_T1A2QR.step

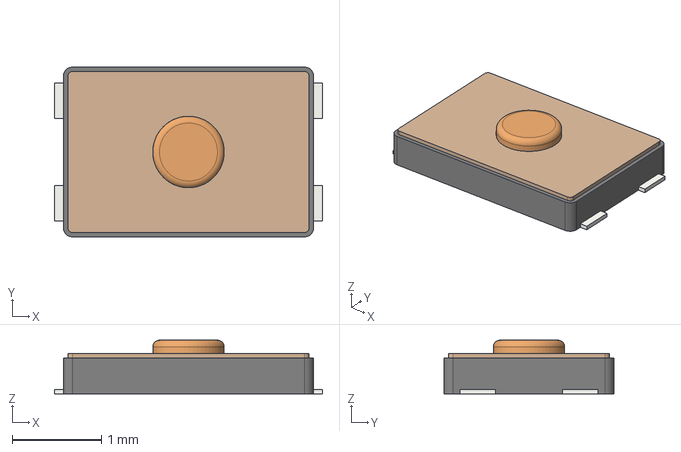
[picture p100: CAD file, 2025-10-04]
marbastlib-main/marbastlib-main/3dmodels/SW_T1A2QR.step
3.00 x 1.90 x 0.6 mm
