ahujaesh/keeb/marbastlib-main/marbastlib-main/3dmodels/holyiot_18010_nRF52840.step

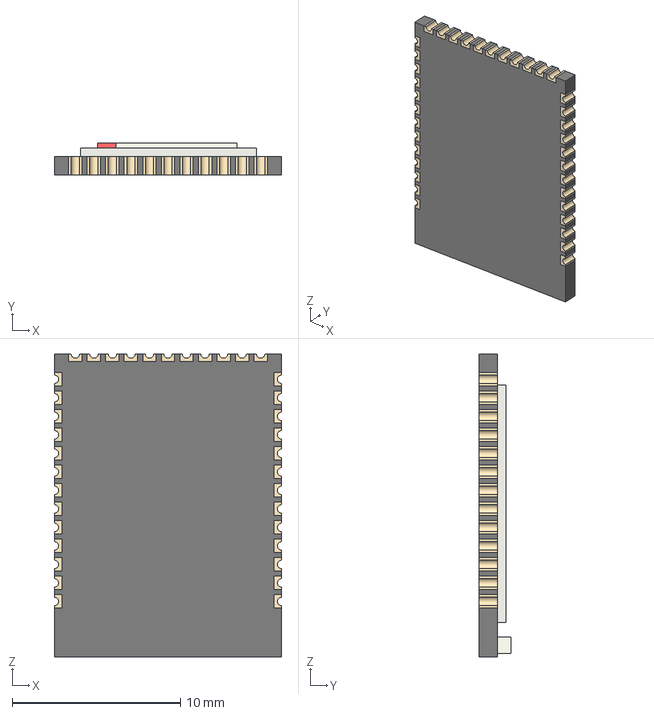
[picture p101: CAD file, 2025-10-04]
marbastlib-main/marbastlib-main/3dmodels/holyiot_18010_nRF52840.step
13.5 x 1.92 x 18.0 mm
