ahujaesh/keeb/marbastlib-main/marbastlib-main/3dmodels/CON_XUNPU_FPC-0.5AL-20PB.step

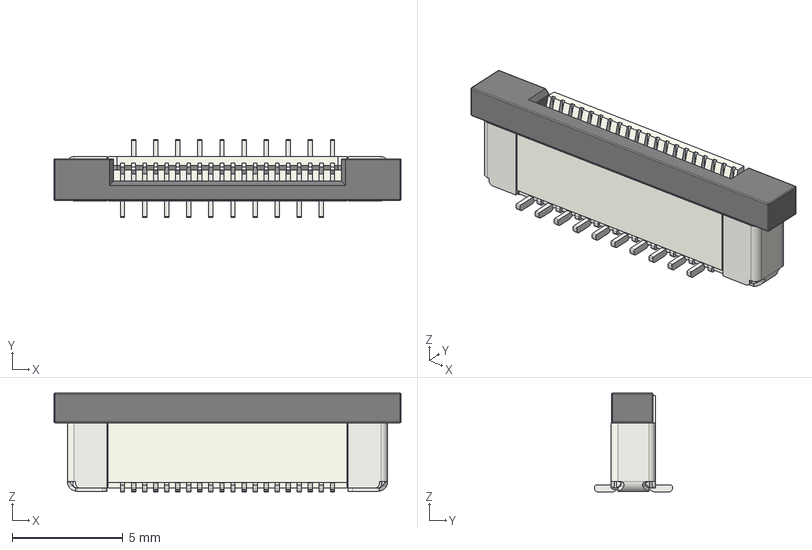
[picture p102: CAD file, 2025-10-04]
marbastlib-main/marbastlib-main/3dmodels/CON_XUNPU_FPC-0.5AL-20PB.step
15.7 x 3.52 x 4.47 mm
