ahujaesh/keeb/marbastlib-main/marbastlib-main/3dmodels/SW_MX6C-K3NB.step

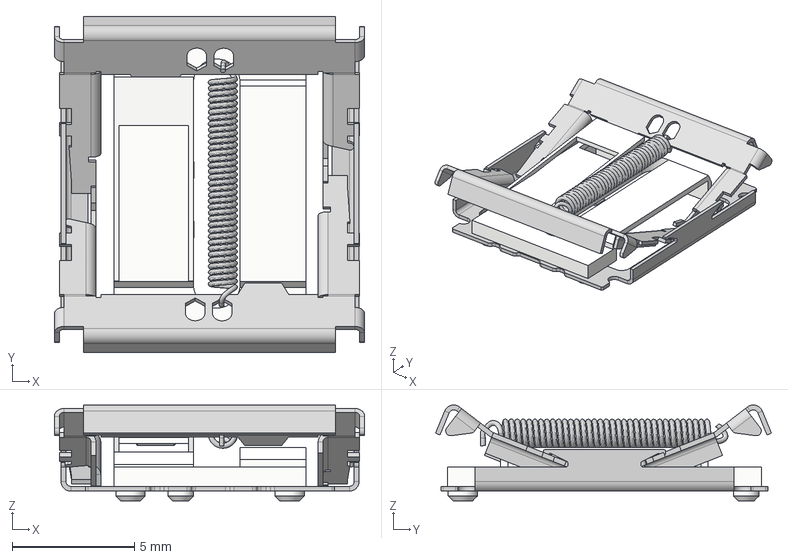
[picture p104: CAD file, 2025-10-04]
marbastlib-main/marbastlib-main/3dmodels/SW_MX6C-K3NB.step
12.7 x 13.8 x 3.93 mm
