ahujaesh/keeb/marbastlib-main/marbastlib-main/3dmodels/ROT_EC11E.step

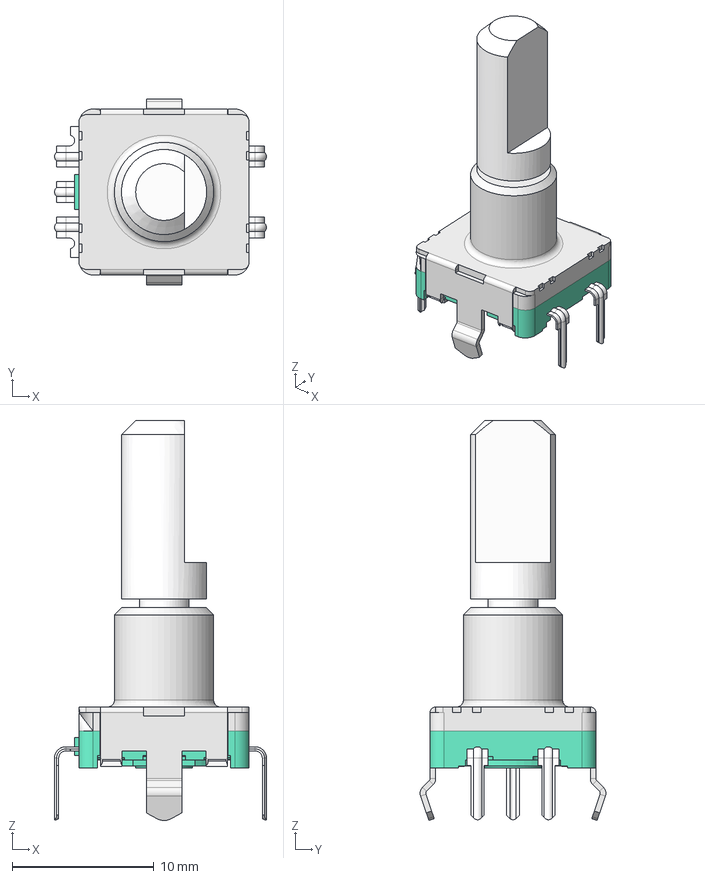
[picture p105: CAD file, 2025-10-04]
marbastlib-main/marbastlib-main/3dmodels/ROT_EC11E.step
14.9 x 13.1 x 28.2 mm
