ahujaesh/keeb/marbastlib-main/marbastlib-main/3dmodels/CON_2121340002.step

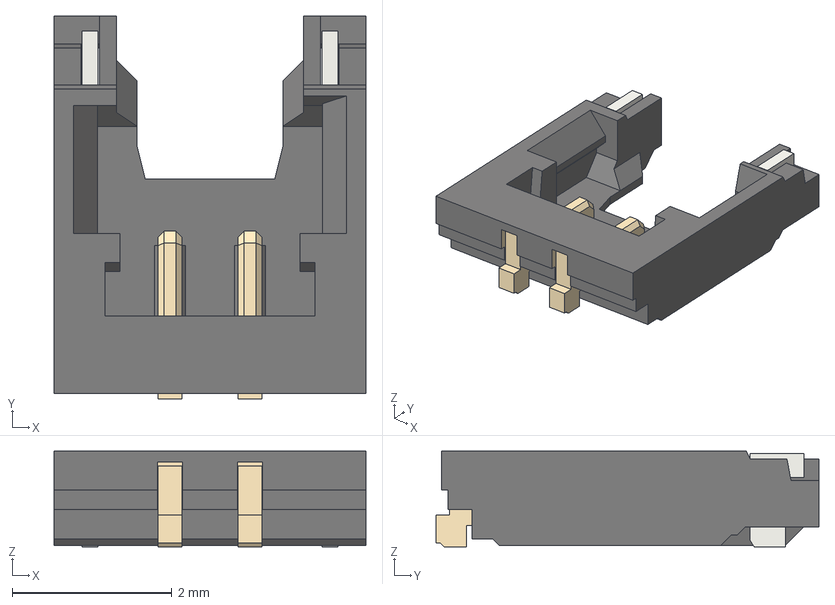
[picture p106: CAD file, 2025-10-04]
marbastlib-main/marbastlib-main/3dmodels/CON_2121340002.step
3.90 x 4.79 x 1.20 mm
