ahujaesh/keeb/marbastlib-main/marbastlib-main/3dmodels/HS_CPG151101S11_MX.step

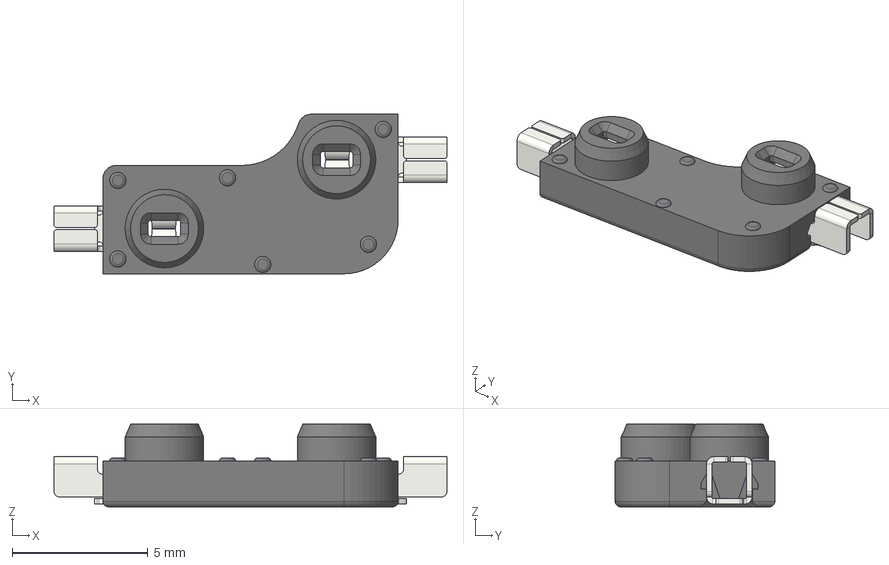
[picture p107: CAD file, 2025-10-04]
marbastlib-main/marbastlib-main/3dmodels/HS_CPG151101S11_MX.step
14.5 x 5.89 x 3.05 mm
Contact x 2
