ahujaesh/keeb/marbastlib-main/marbastlib-main/3dmodels/CON_HC-PBB40C-10DS-0.4V-2.0-02.step

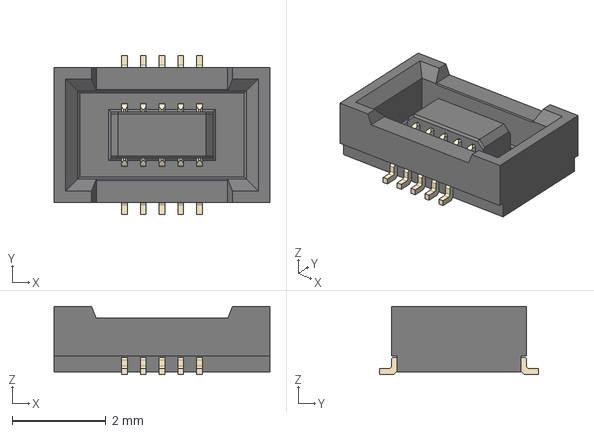
[picture p108: CAD file, 2025-10-04]
marbastlib-main/marbastlib-main/3dmodels/CON_HC-PBB40C-10DS-0.4V-2.0-02.step
4.60 x 3.38 x 1.45 mm
