ahujaesh/keeb/marbastlib-main/marbastlib-main/3dmodels/LED_WS2812_4020.step

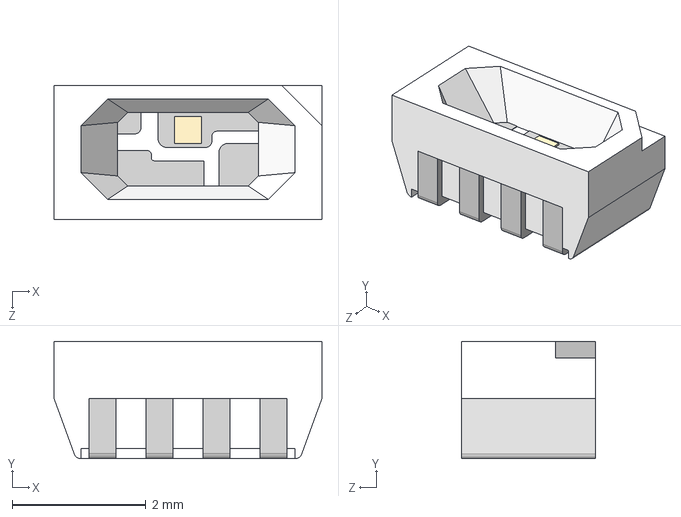
[picture p109: CAD file, 2025-10-04]
marbastlib-main/marbastlib-main/3dmodels/LED_WS2812_4020.step
4.00 x 1.75 x 2.00 mm
