ahujaesh/keeb/marbastlib-main/marbastlib-main/3dmodels/CON_BM02B-ACHSS.step

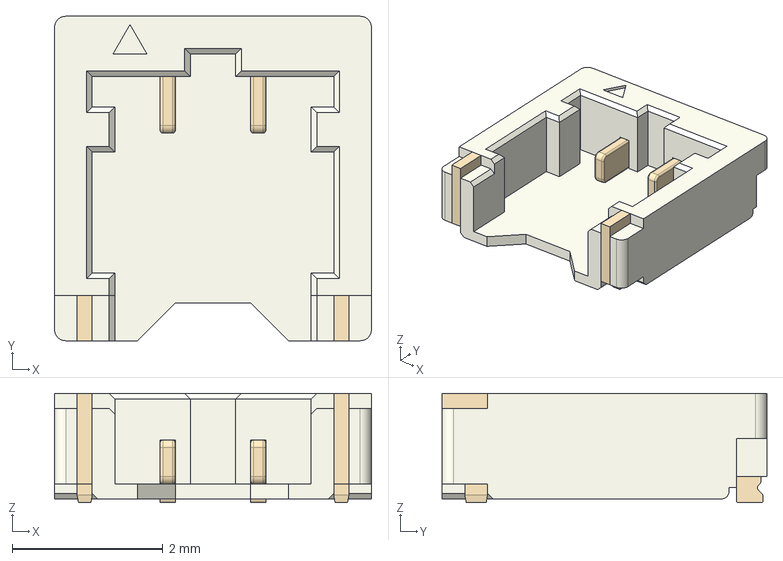
[picture p110: CAD file, 2025-10-04]
marbastlib-main/marbastlib-main/3dmodels/CON_BM02B-ACHSS.step
4.20 x 4.30 x 1.45 mm
