ahujaesh/keeb/marbastlib-main/marbastlib-main/3dmodels/CON_TYPE-C-31-M-14.step

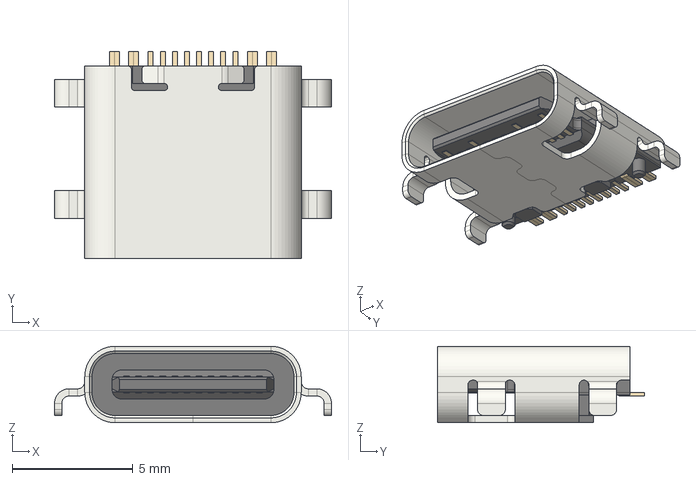
[picture p111: CAD file, 2025-10-04]
marbastlib-main/marbastlib-main/3dmodels/CON_TYPE-C-31-M-14.step
11.5 x 8.56 x 3.16 mm
Shroud
Plastic Body & Connector
